zaidh-mech/project-zeno/assets/photos/20250816_165505.jpg

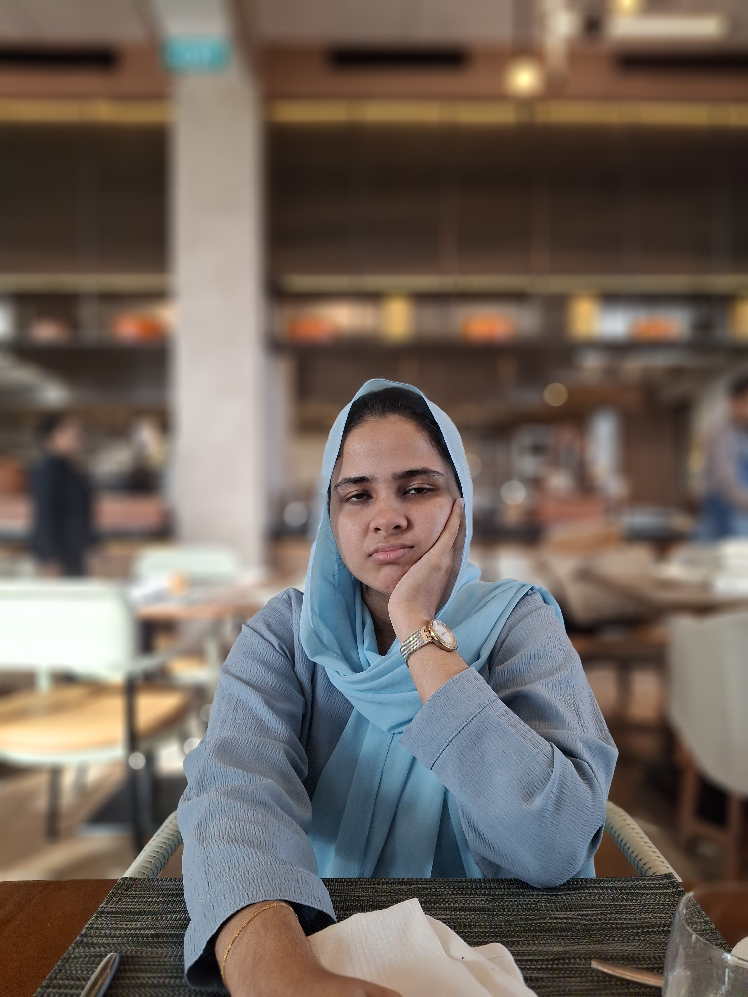
assets/photos/20250816_165505.jpg
