zaidh-mech/project-zeno/assets/photos/20250816_165511.jpg

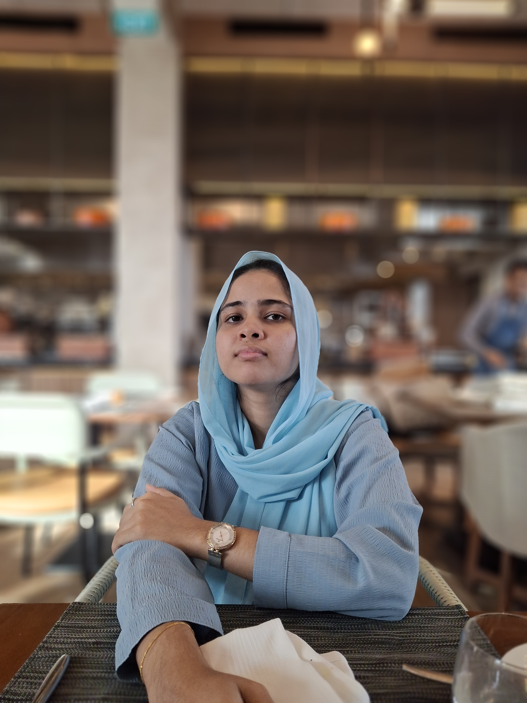
assets/photos/20250816_165511.jpg
