zaidh-mech/project-zeno/assets/photos/20250816_165538.jpg

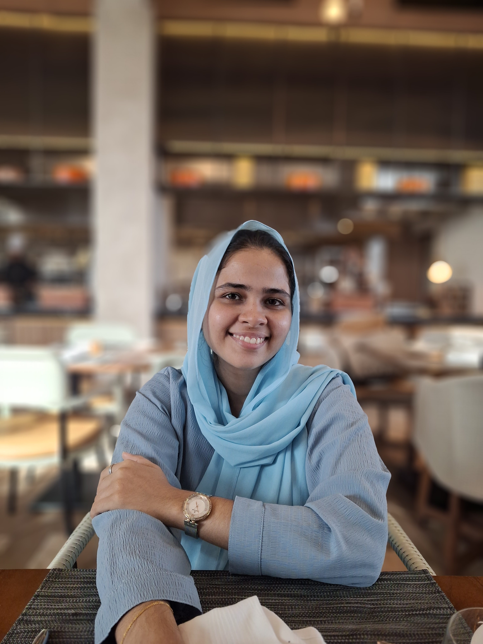
assets/photos/20250816_165538.jpg
