zaidh-mech/project-zeno/assets/photos/20250816_171857.jpg

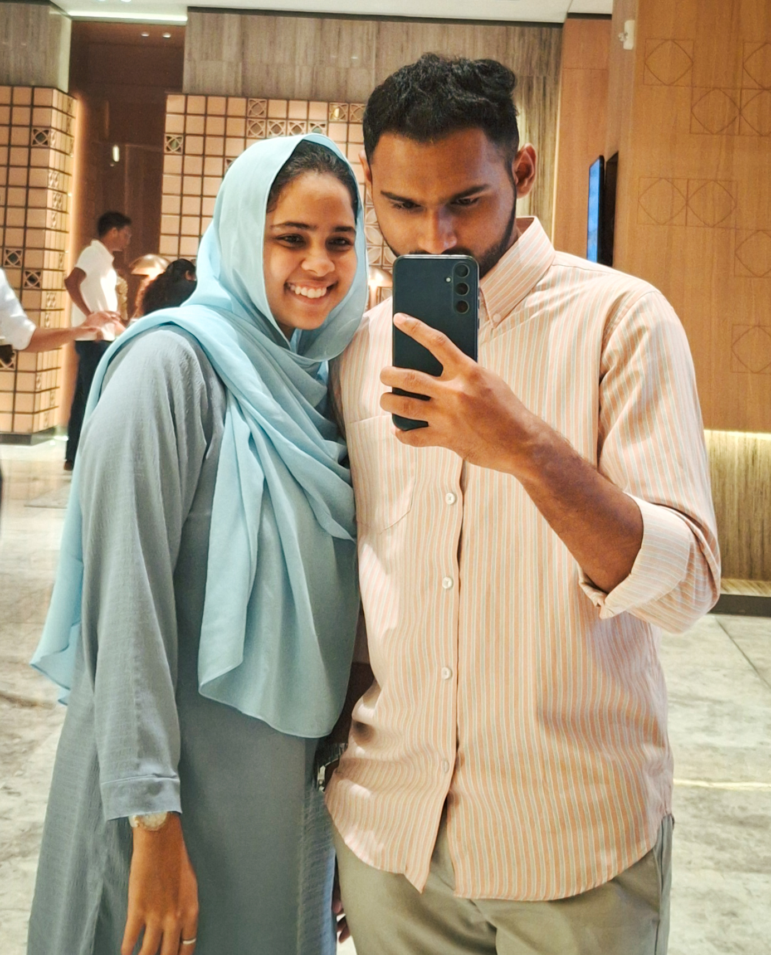
assets/photos/20250816_171857.jpg
