zaidh-mech/project-zeno/assets/photos/IMG-20231231-WA0020.jpg

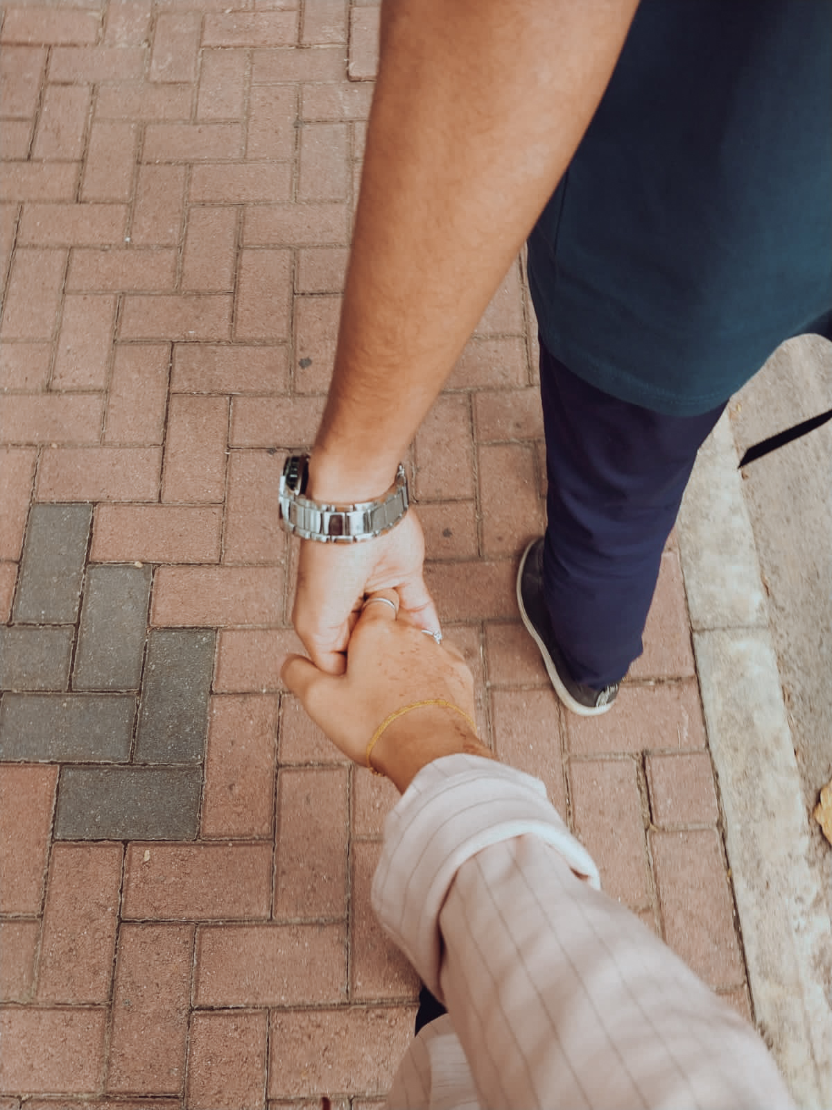
assets/photos/IMG-20231231-WA0020.jpg
