zaidh-mech/project-zeno/assets/photos/IMG-20240403-WA0015.jpg

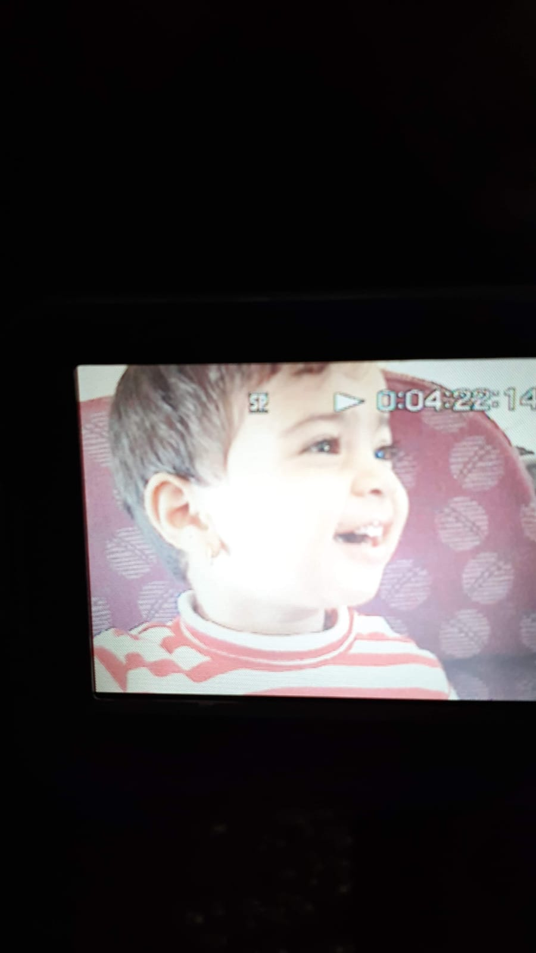
assets/photos/IMG-20240403-WA0015.jpg
