zaidh-mech/project-zeno/assets/photos/IMG-20240619-WA0054.jpg

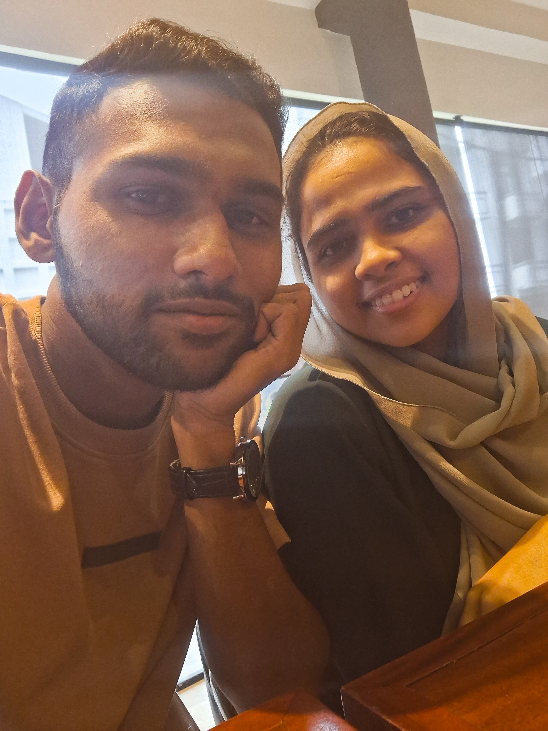
assets/photos/IMG-20240619-WA0054.jpg
