zaidh-mech/project-zeno/assets/photos/IMG-20241203-WA0028.jpg

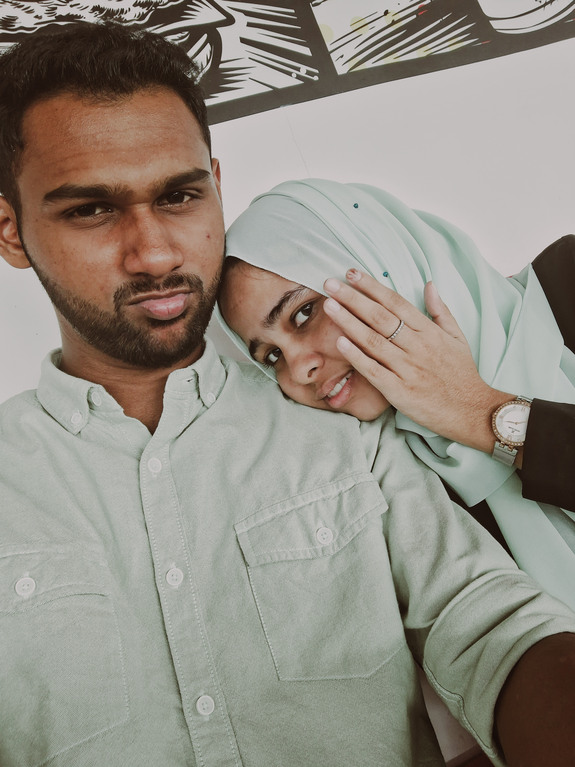
assets/photos/IMG-20241203-WA0028.jpg
