zaidh-mech/project-zeno/assets/photos/Snapchat-101565929.jpg

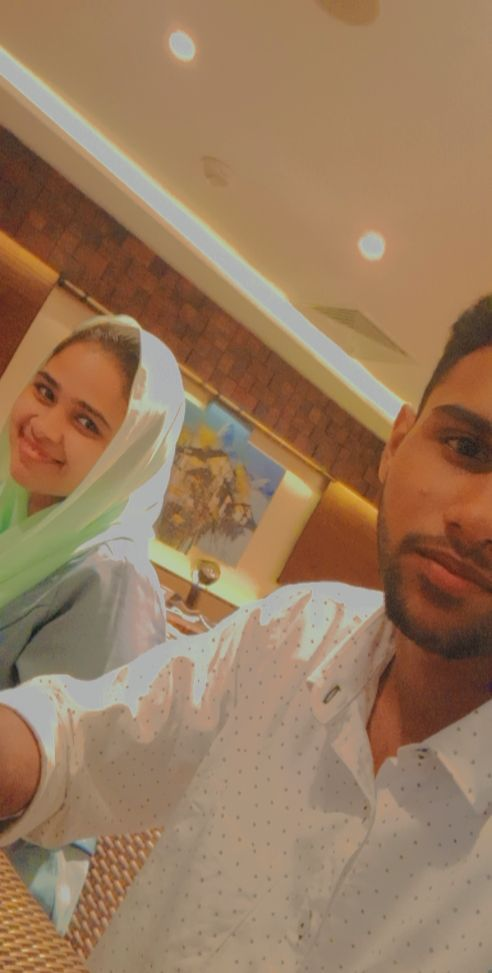
assets/photos/Snapchat-101565929.jpg
