zaidh-mech/project-zeno/assets/photos/Snapchat-125031793.jpg

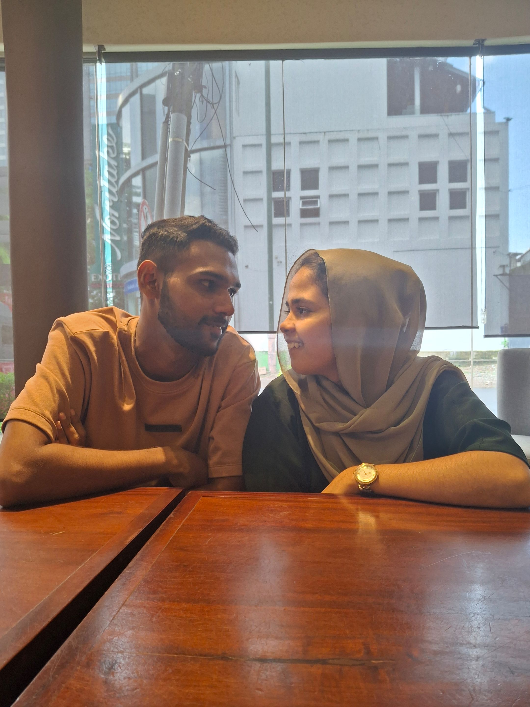
assets/photos/Snapchat-125031793.jpg
