zaidh-mech/project-zeno/assets/photos/Snapchat-195665847.jpg

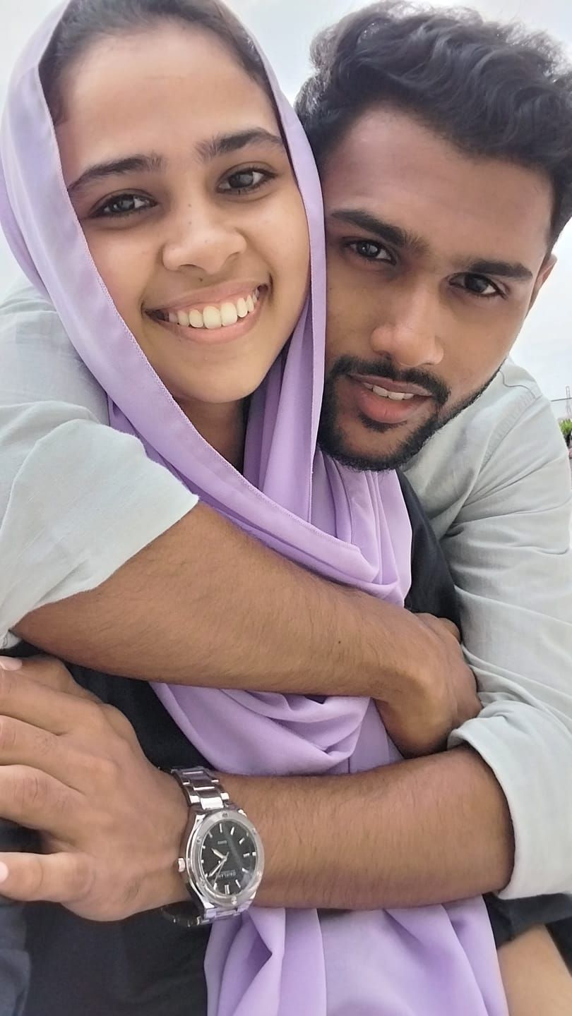
assets/photos/Snapchat-195665847.jpg
