zaidh-mech/project-zeno/assets/photos/Snapchat-261854260.jpg

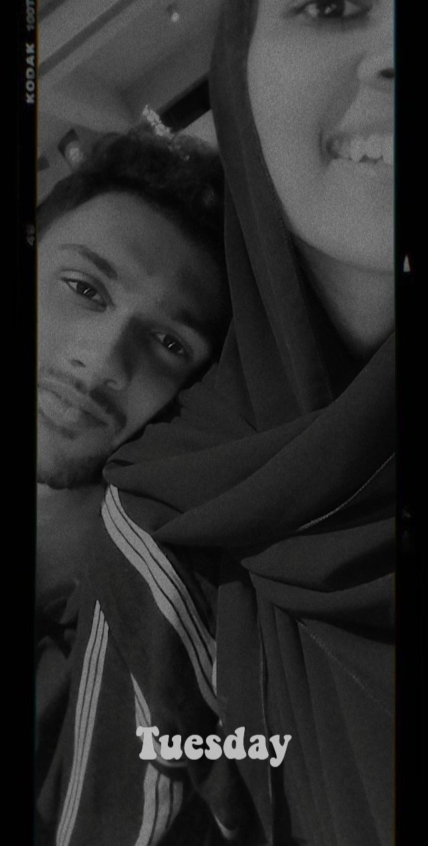
assets/photos/Snapchat-261854260.jpg
