zaidh-mech/project-zeno/assets/photos/Snapchat-302030129.jpg

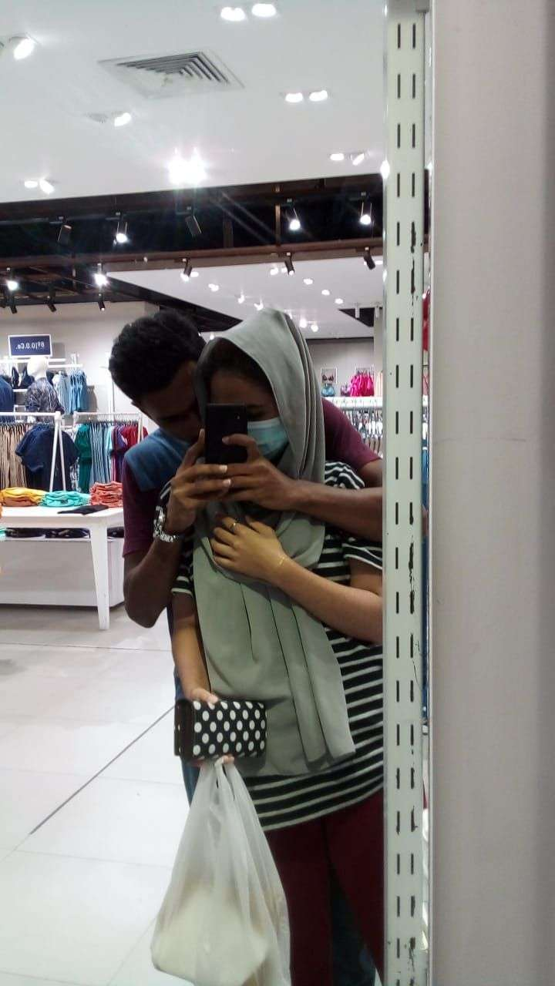
assets/photos/Snapchat-302030129.jpg
