zaidh-mech/project-zeno/assets/photos/Snapchat-348084734.jpg

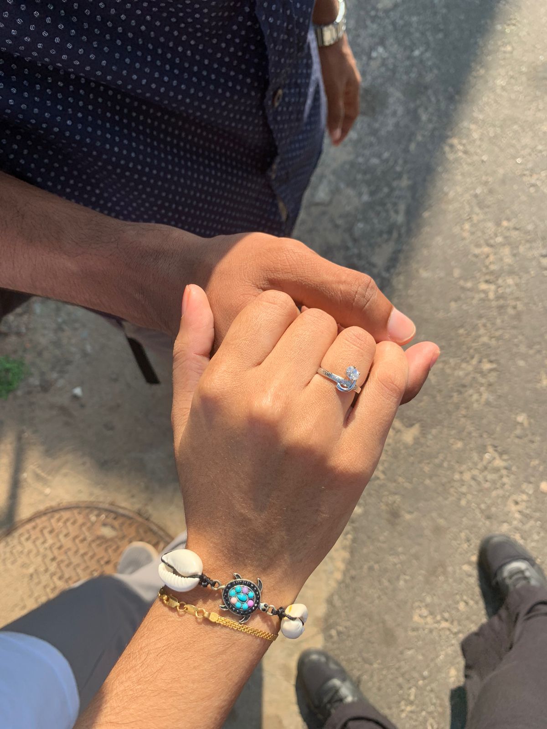
assets/photos/Snapchat-348084734.jpg
