zaidh-mech/project-zeno/assets/photos/Snapchat-446111282.jpg

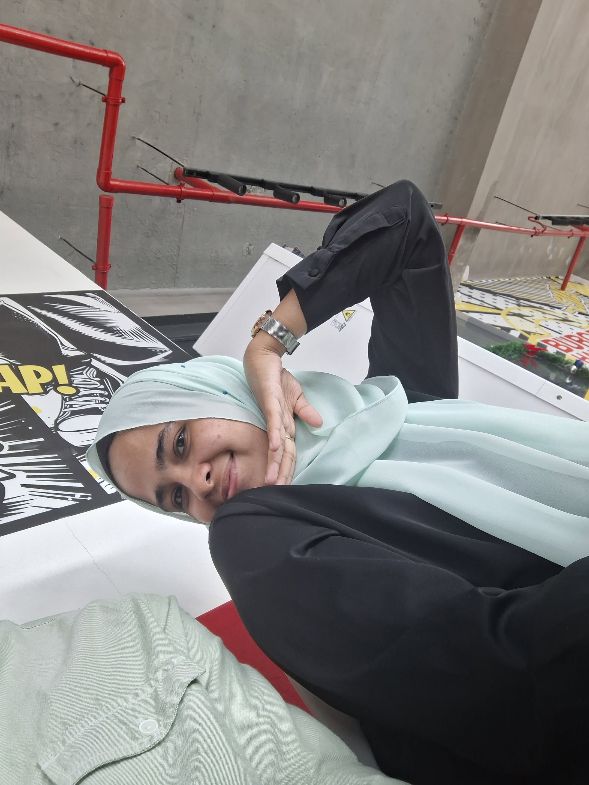
assets/photos/Snapchat-446111282.jpg
