zaidh-mech/project-zeno/assets/photos/Snapchat-537881204.jpg

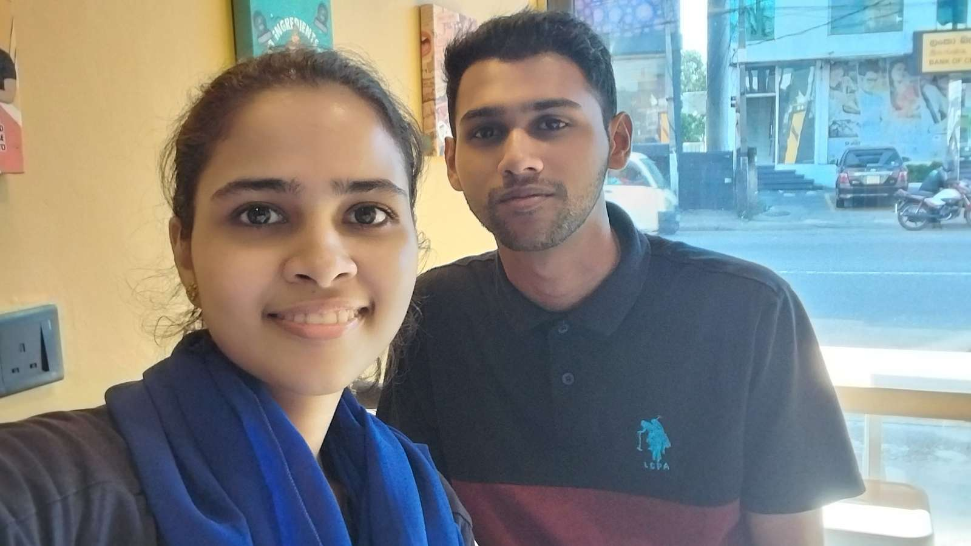
assets/photos/Snapchat-537881204.jpg
