zaidh-mech/project-zeno/assets/photos/Snapchat-637943176.jpg

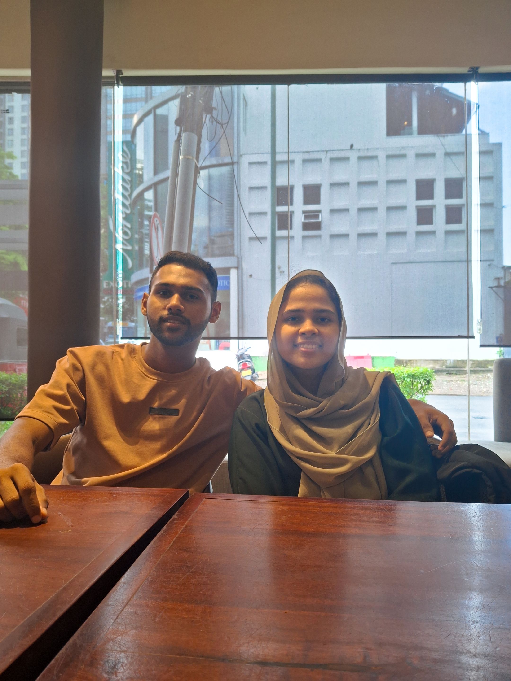
assets/photos/Snapchat-637943176.jpg
