zaidh-mech/project-zeno/assets/photos/Snapchat-755938516.jpg

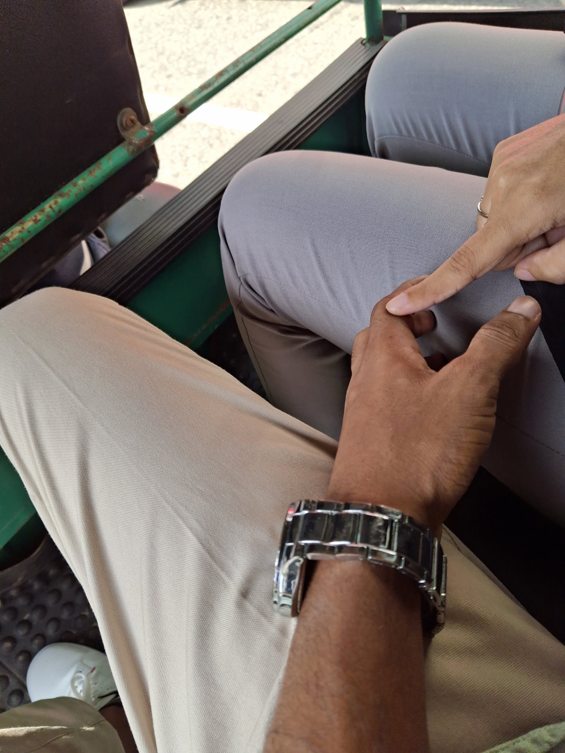
assets/photos/Snapchat-755938516.jpg
