zaidh-mech/project-zeno/assets/photos/Snapchat-759489266.jpg

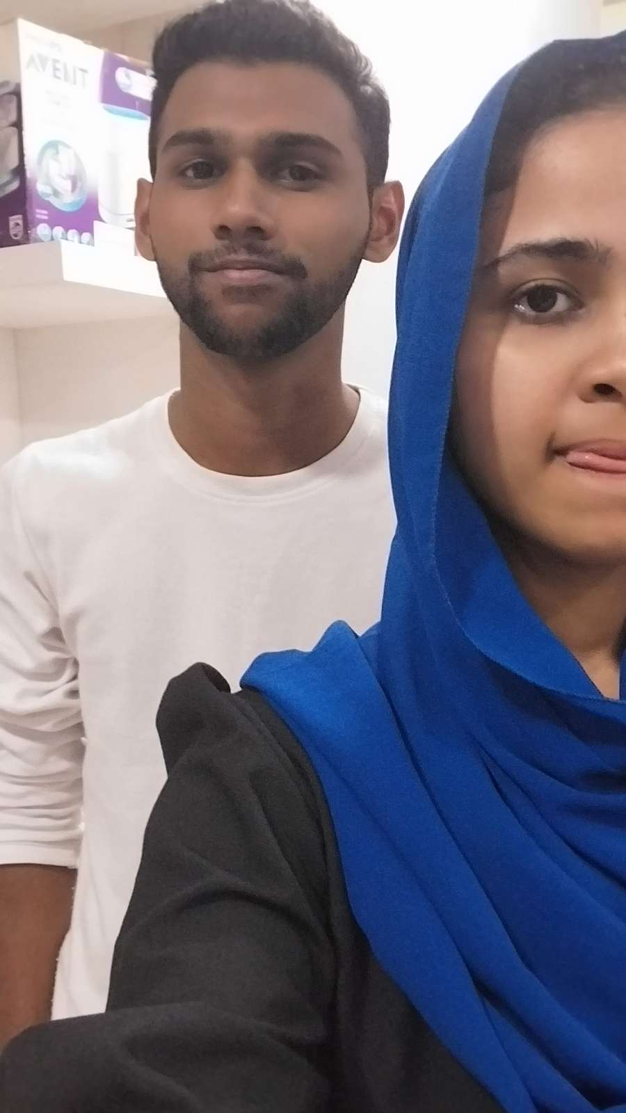
assets/photos/Snapchat-759489266.jpg
