zaidh-mech/project-zeno/assets/photos/Snapchat-868171429.jpg

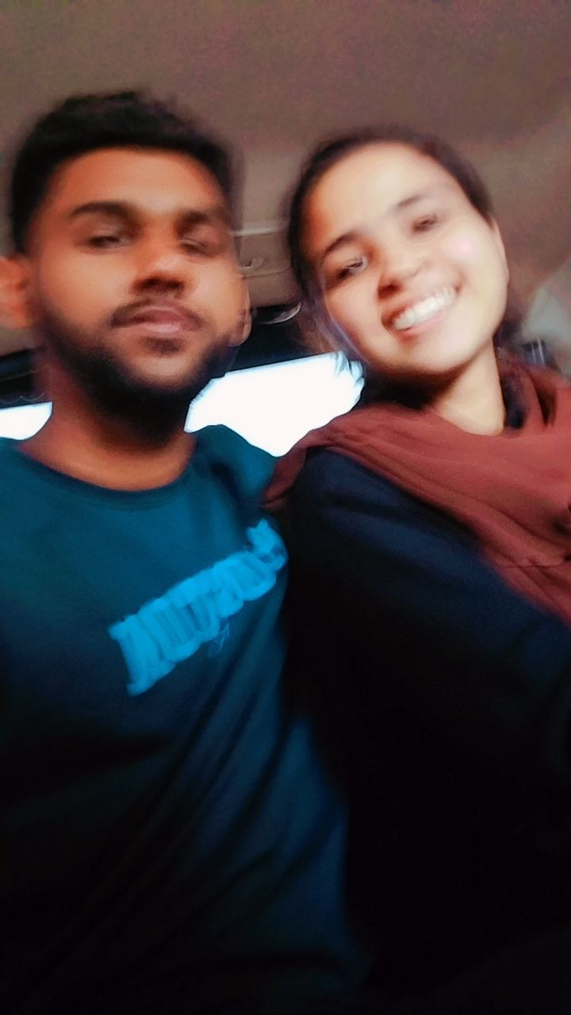
assets/photos/Snapchat-868171429.jpg
