zaidh-mech/project-zeno/assets/photos/Snapchat-1000629672.jpg

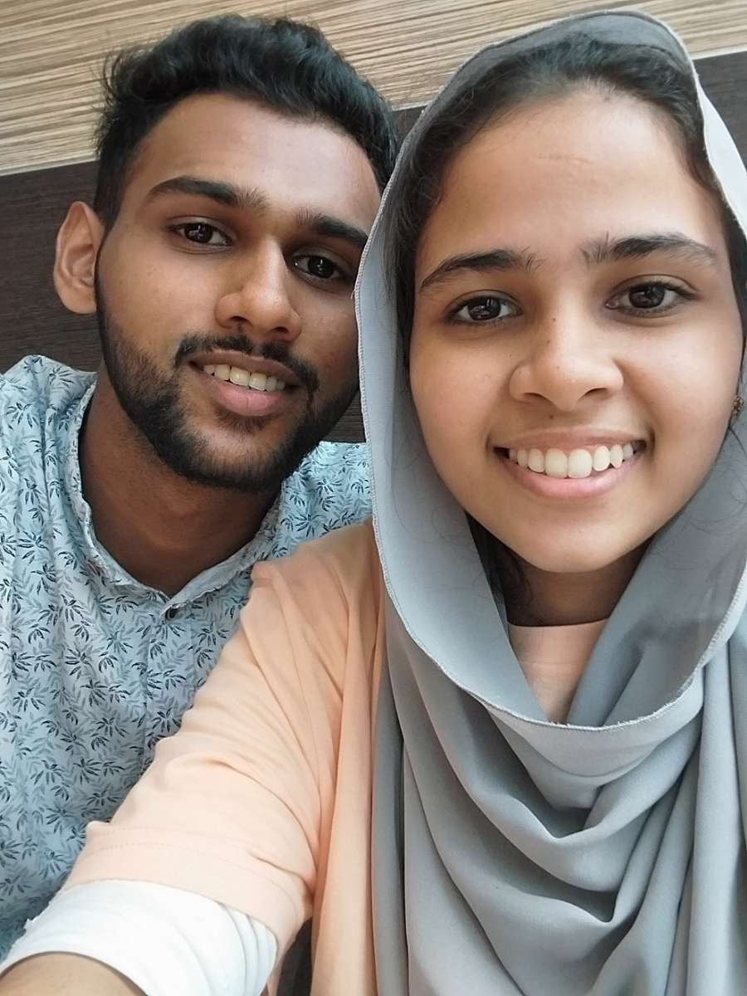
assets/photos/Snapchat-1000629672.jpg
