zaidh-mech/project-zeno/assets/photos/Snapchat-1169559502.jpg

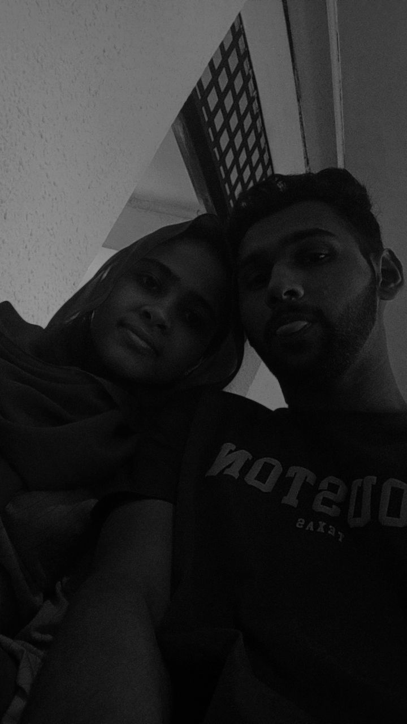
assets/photos/Snapchat-1169559502.jpg
