zaidh-mech/project-zeno/assets/photos/Snapchat-1356561112.jpg

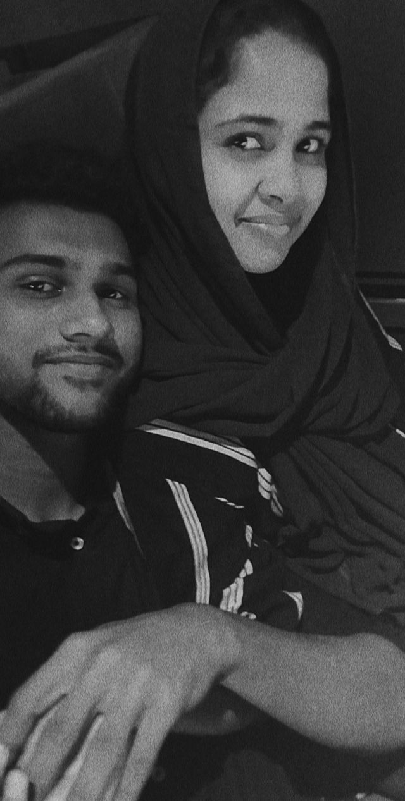
assets/photos/Snapchat-1356561112.jpg
