zaidh-mech/project-zeno/assets/photos/Snapchat-1552943826.jpg

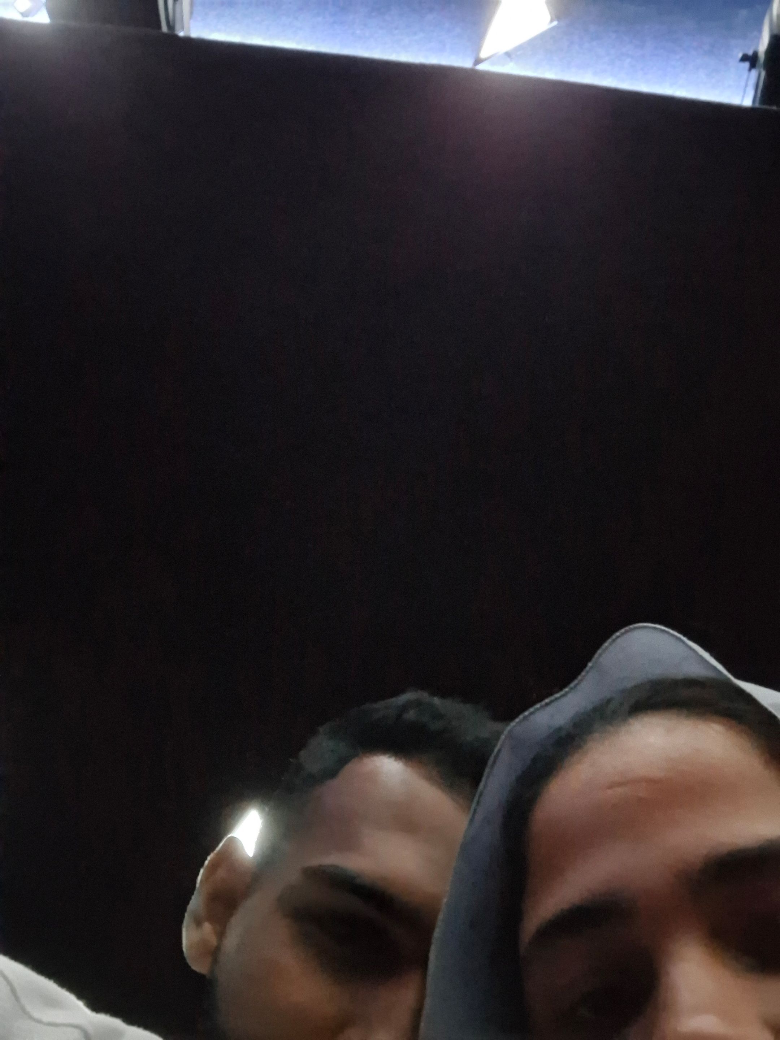
assets/photos/Snapchat-1552943826.jpg
