zaidh-mech/project-zeno/assets/photos/Snapchat-1667827849.jpg

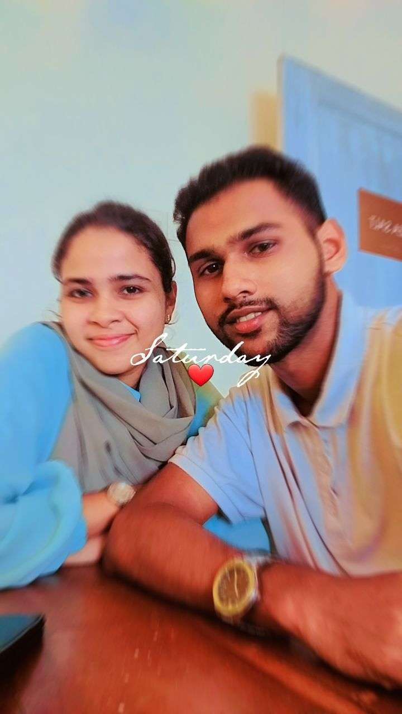
assets/photos/Snapchat-1667827849.jpg
