zaidh-mech/project-zeno/assets/photos/Snapchat-1719029851.jpg

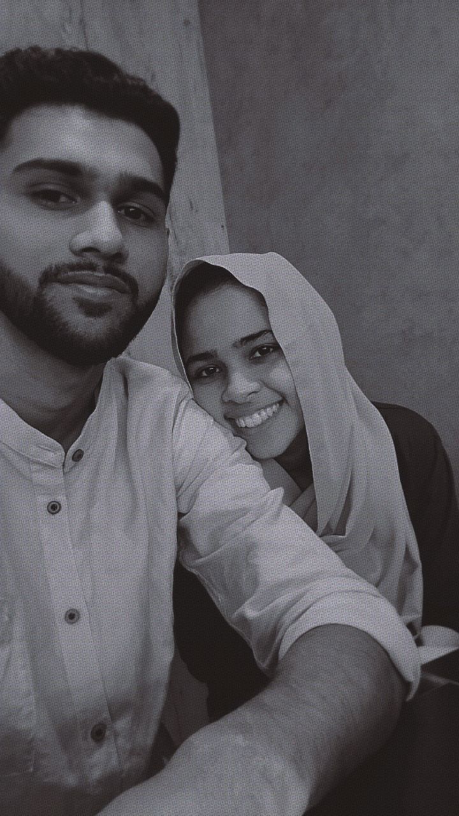
assets/photos/Snapchat-1719029851.jpg
