zaidh-mech/project-zeno/assets/photos/Snapchat-1755354417.jpg

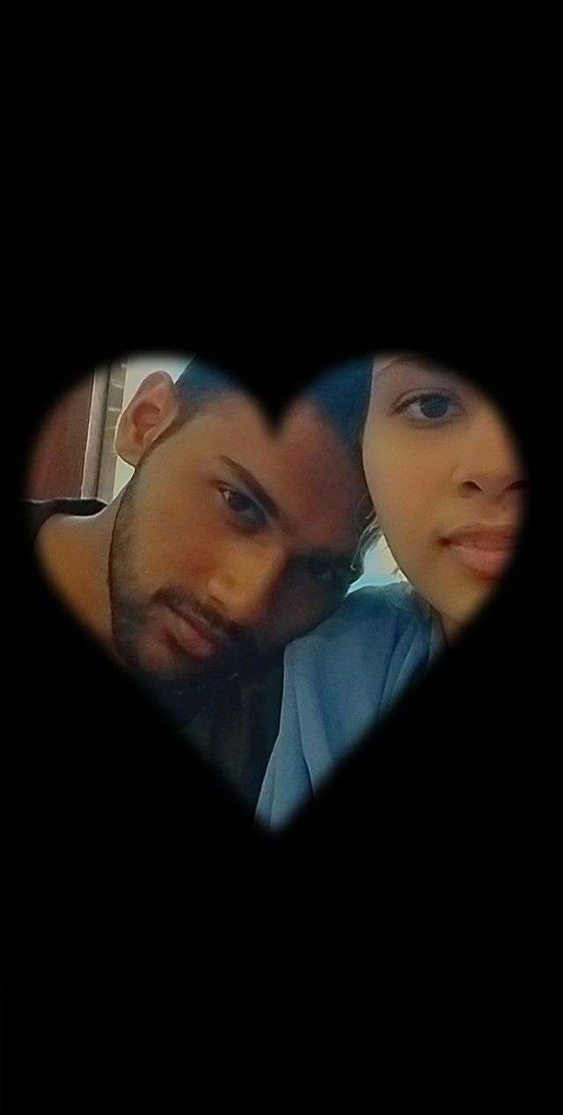
assets/photos/Snapchat-1755354417.jpg
