zaidh-mech/project-zeno/assets/photos/Snapchat-1938630685.jpg

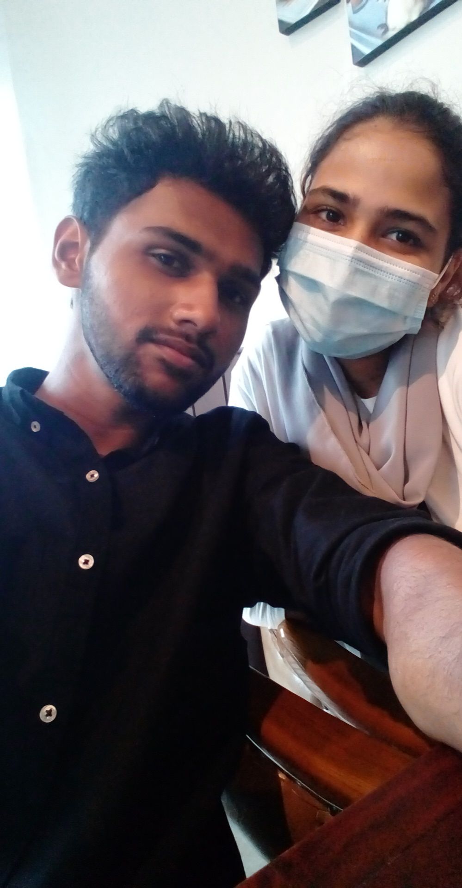
assets/photos/Snapchat-1938630685.jpg
