zaidh-mech/project-zeno/assets/photos/Snapchat-1975126700.jpg

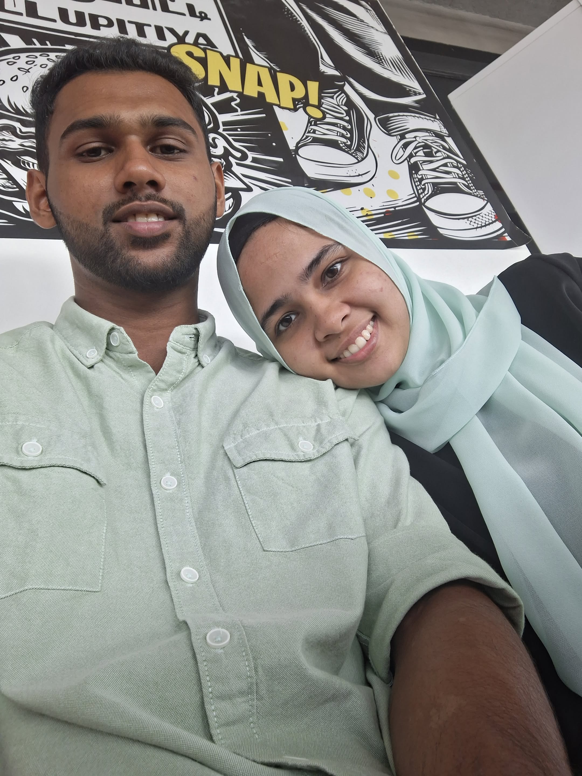
assets/photos/Snapchat-1975126700.jpg
