zaidh-mech/project-zeno/assets/photos/Snapchat-2021210493.jpg

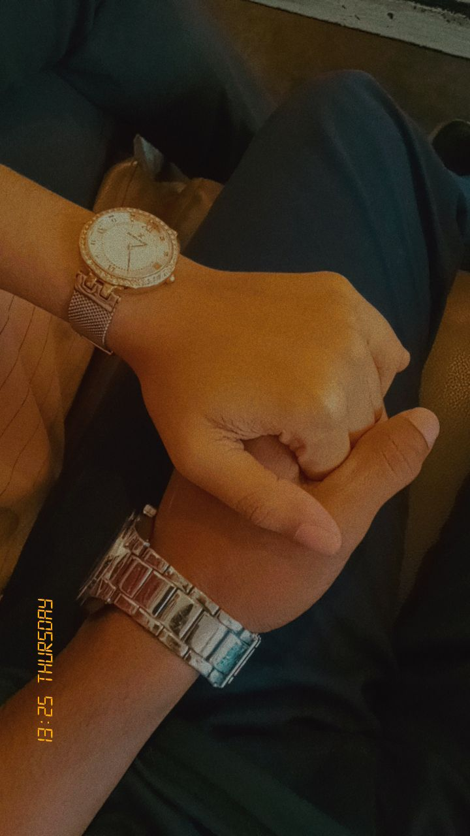
assets/photos/Snapchat-2021210493.jpg
