zaidh-mech/project-zeno/assets/photos/Snapchat-2032227030.jpg

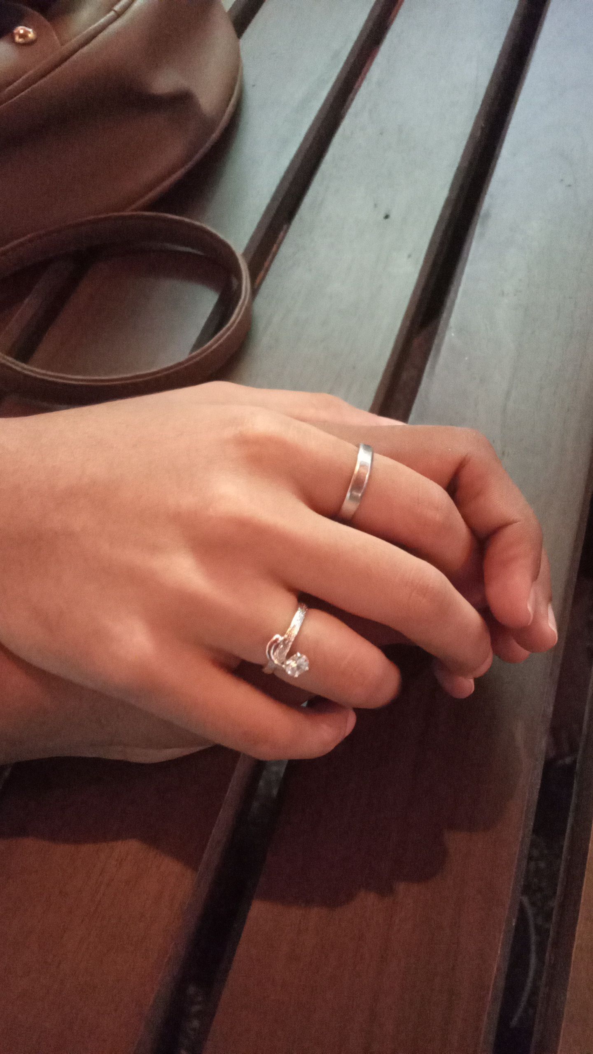
assets/photos/Snapchat-2032227030.jpg
