zaidh-mech/project-zeno/assets/photos/Snapchat-2075881520.jpg

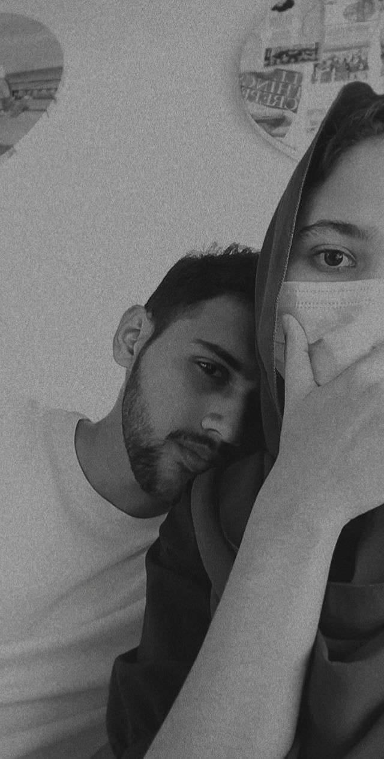
assets/photos/Snapchat-2075881520.jpg
