zaidh-mech/project-zeno/assets/screenshots/Screenshot 2026-09-28 134337.png

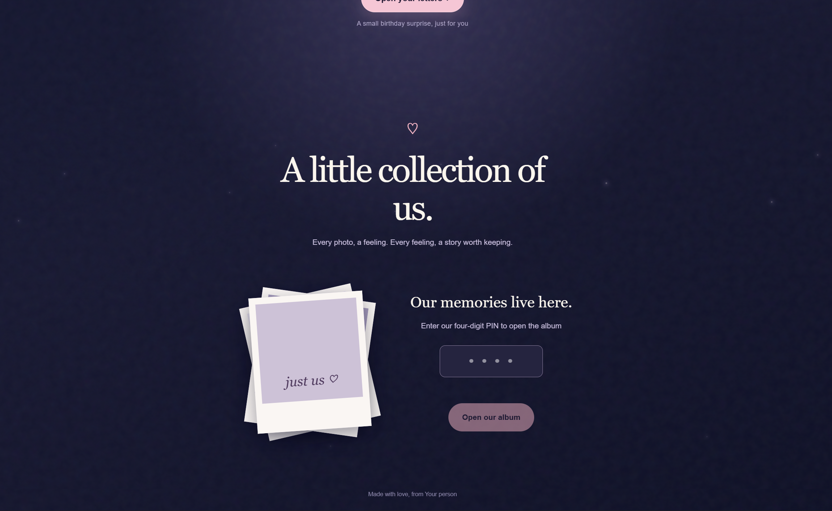
assets/screenshots/Screenshot 2026-09-28 134337.png
