zaidh-mech/project-zeno/assets/screenshots/Screenshot 2026-10-01 145643.png

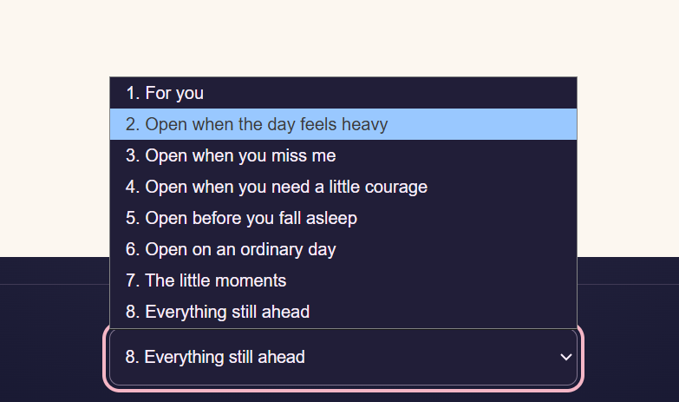
assets/screenshots/Screenshot 2026-10-01 145643.png
