zaidh-mech/project-zeno/assets/screenshots/Screenshot 2026-10-02 182400.png

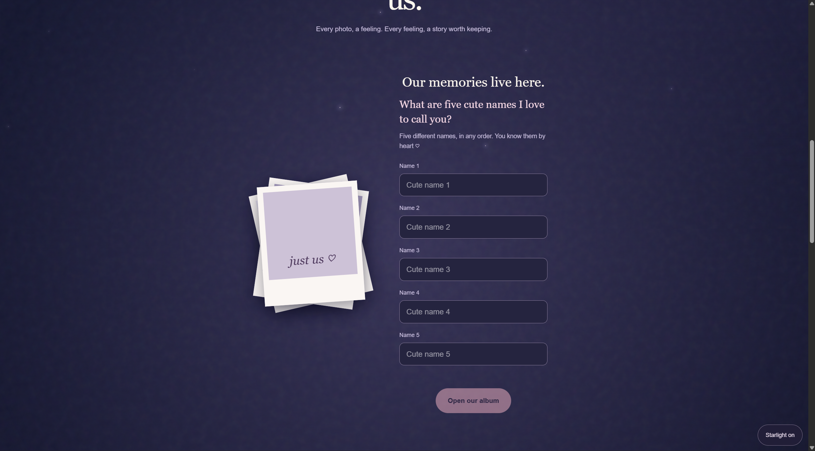
assets/screenshots/Screenshot 2026-10-02 182400.png
