zaidh-mech/project-zeno/companion/drawings/02_Rear_ports.png

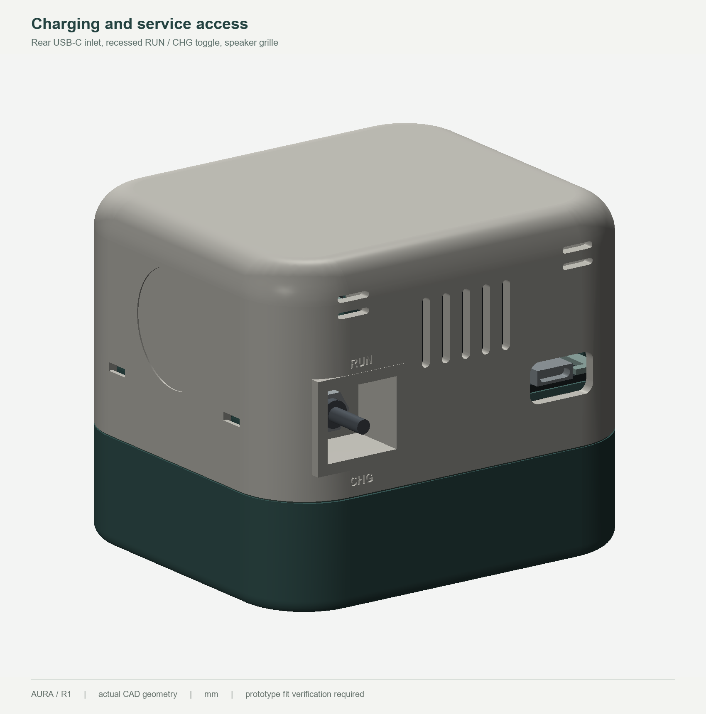
companion/drawings/02_Rear_ports.png
