zaidh-mech/project-zeno/companion/drawings/03_Internal_layout.png

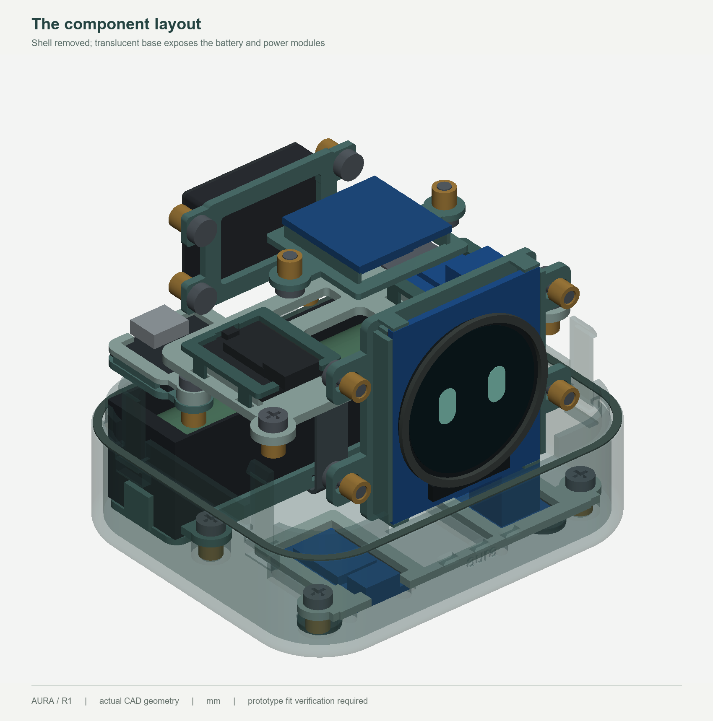
companion/drawings/03_Internal_layout.png
