zaidh-mech/project-zeno/companion/drawings/04_Exploded.png

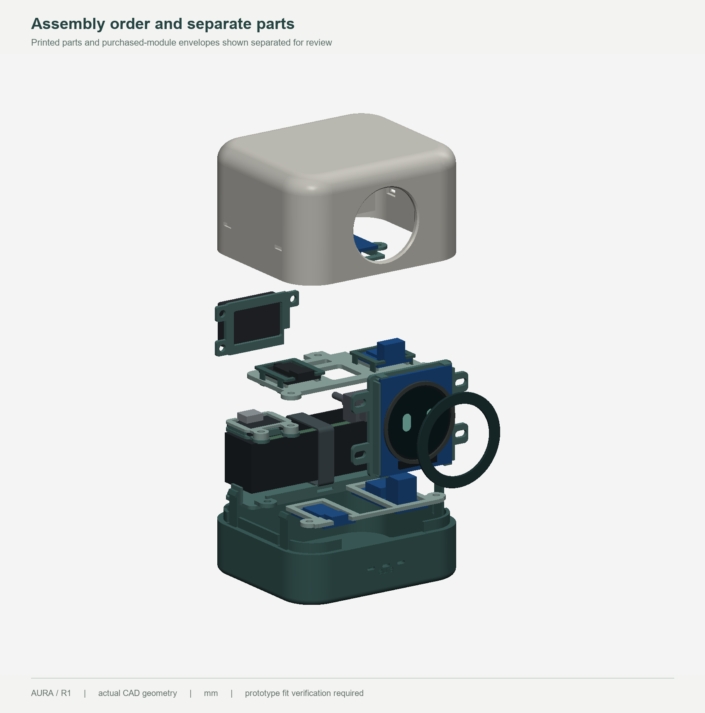
companion/drawings/04_Exploded.png
