zaidh-mech/project-zeno/companion/drawings/05_Cutaway.png

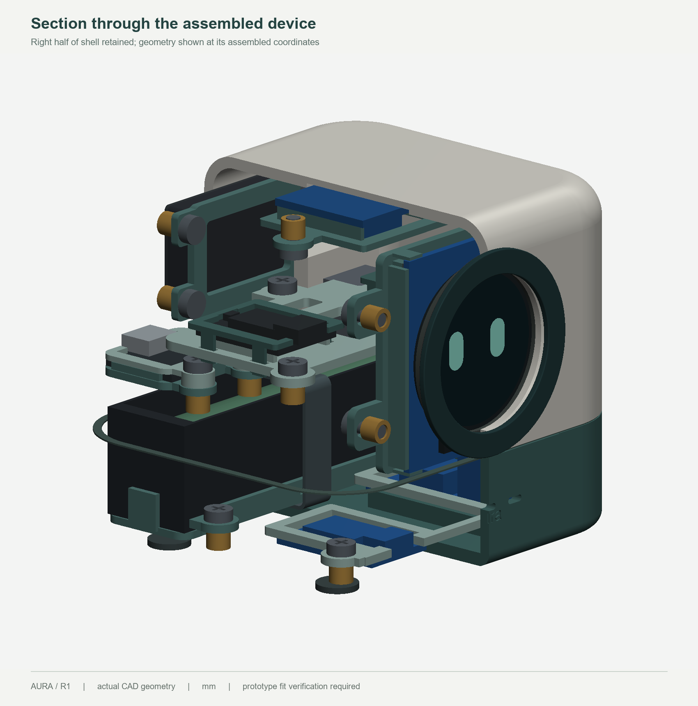
companion/drawings/05_Cutaway.png
