zaidh-mech/project-zeno/companion/drawings/06_General_arrangement.png

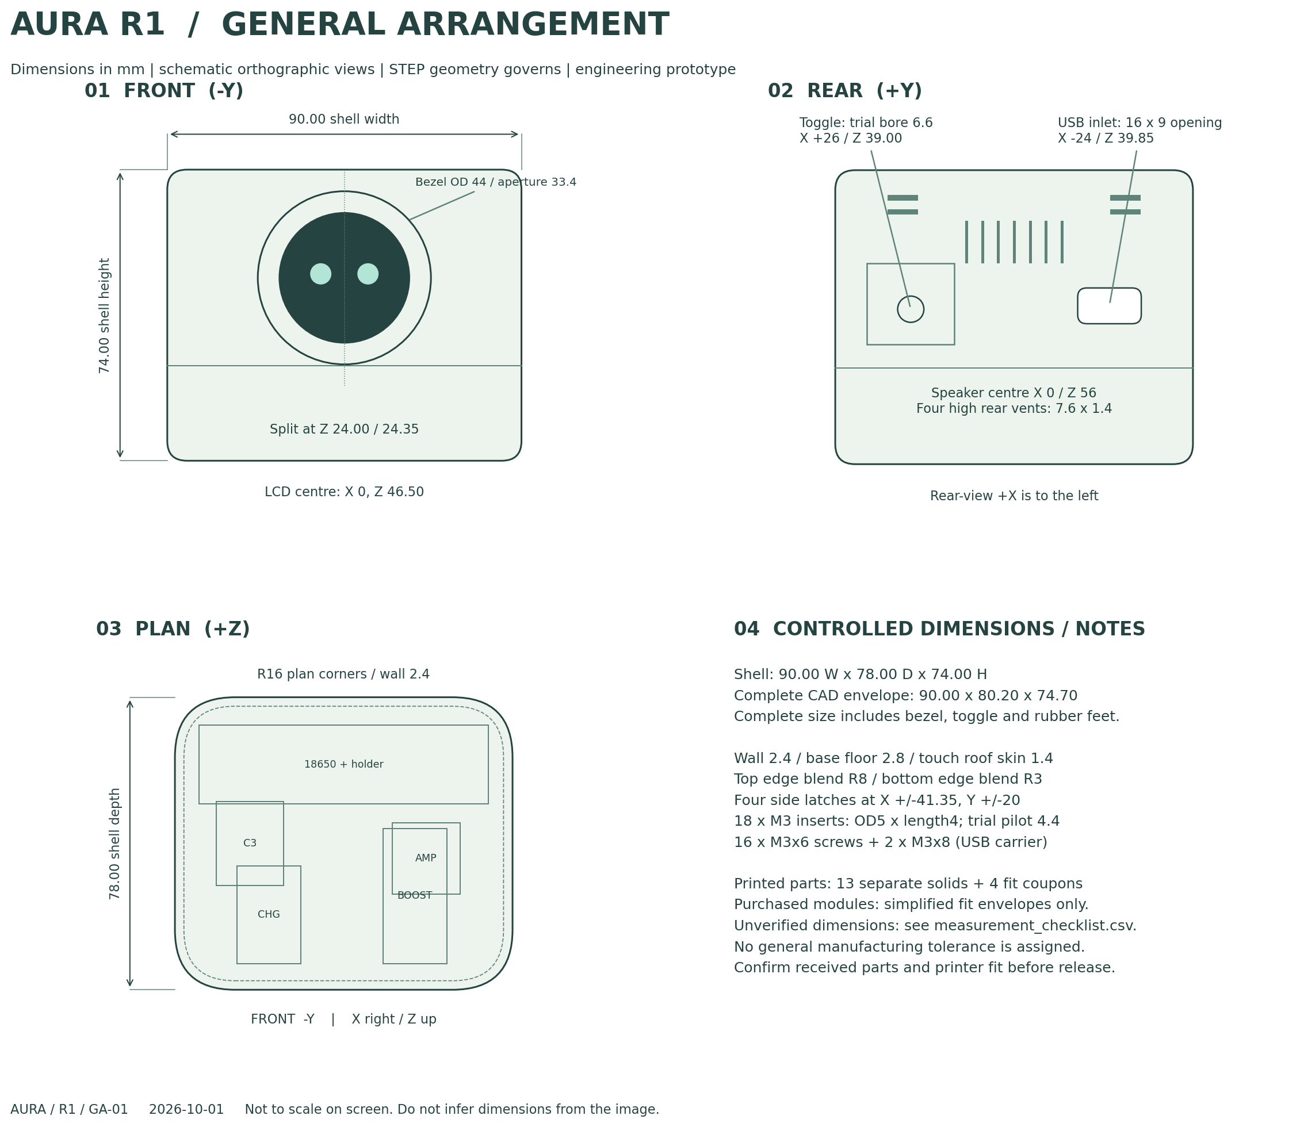
companion/drawings/06_General_arrangement.png
