zaidh-mech/project-zeno/companion/drawings/07_Snap_and_insert_details.png

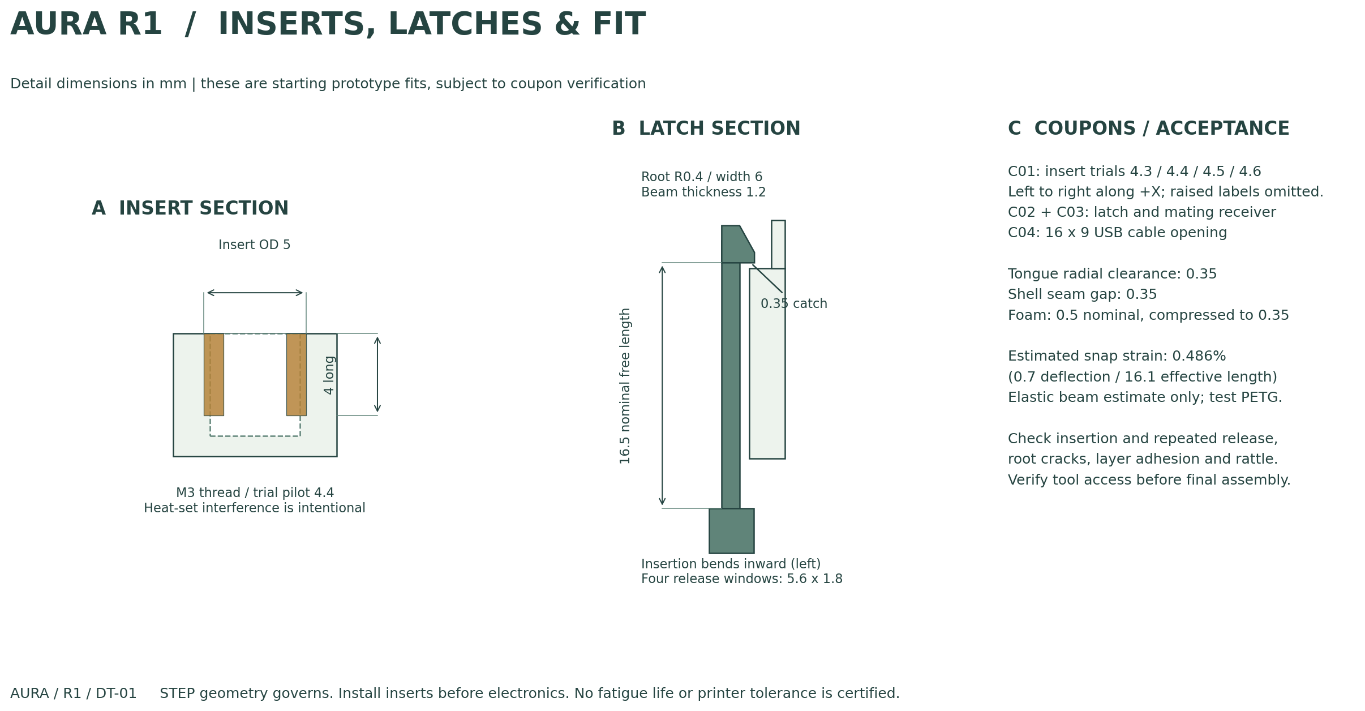
companion/drawings/07_Snap_and_insert_details.png
