zaidh-mech/project-zeno/companion/drawings/08_Power_connections.png

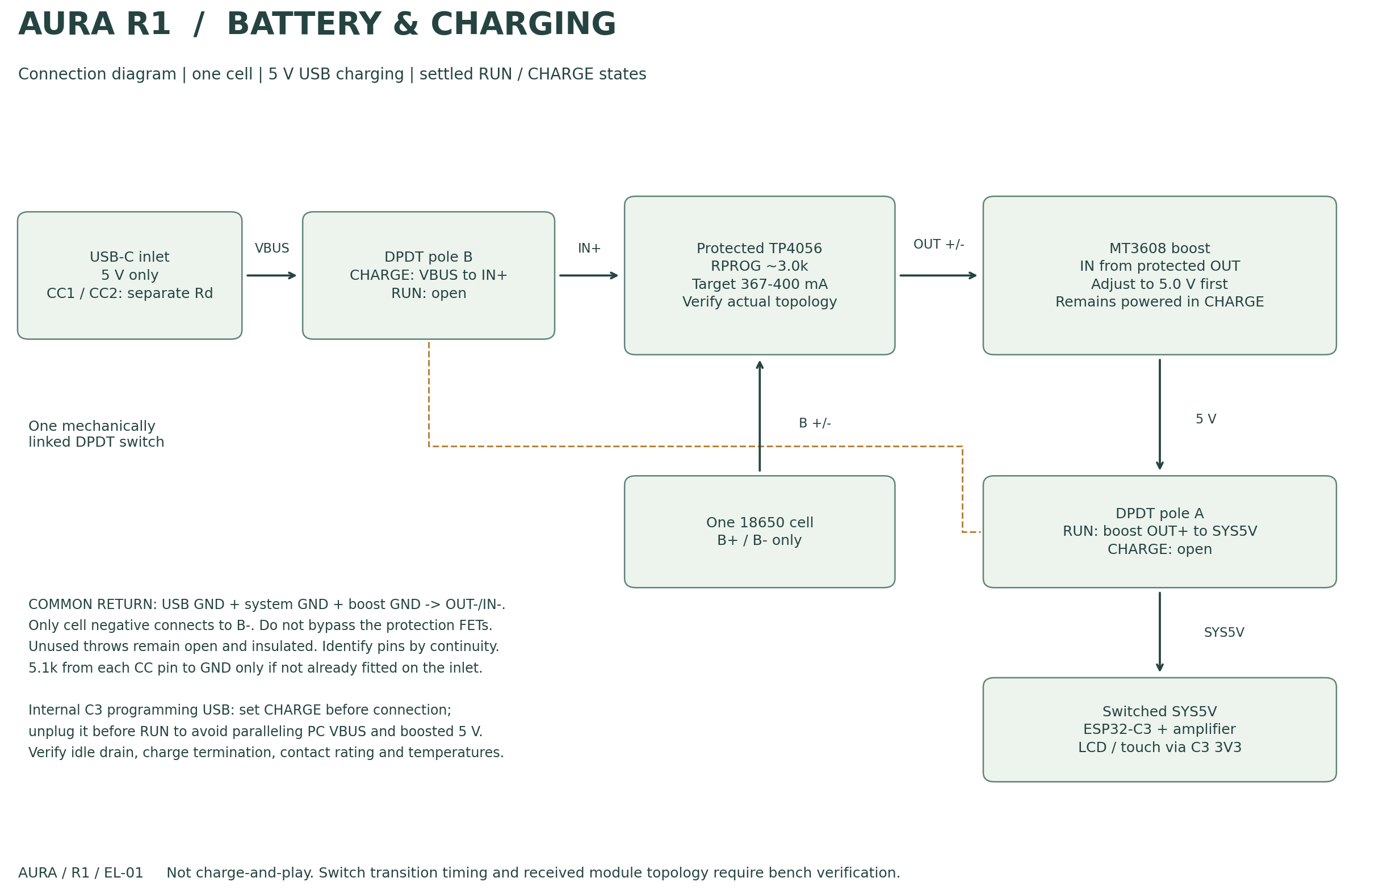
companion/drawings/08_Power_connections.png
