zaidh-mech/project-zeno/companion/parts/coupons/C01_Insert_bores_4p3_4p4_4p5_4p6.step

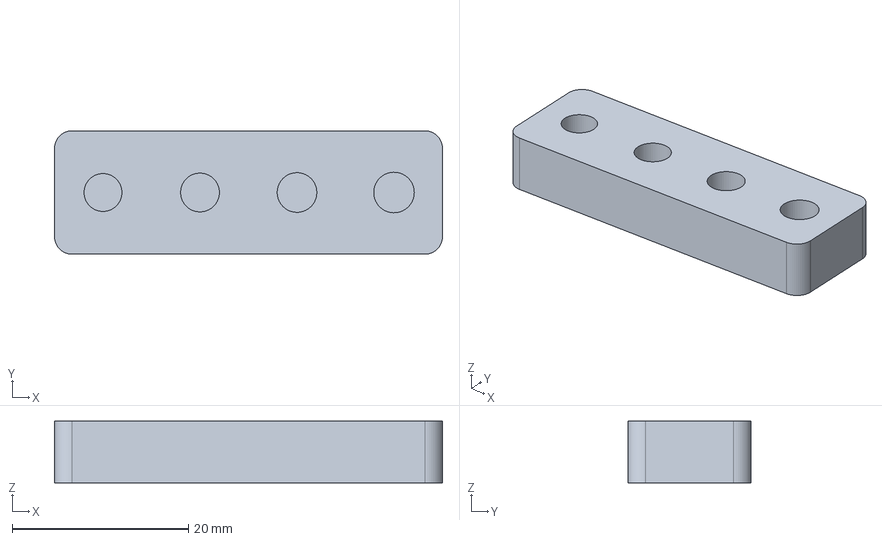
[picture p69: CAD file, 2026-10-05]
companion/parts/coupons/C01_Insert_bores_4p3_4p4_4p5_4p6.step
44.0 x 14.0 x 7.00 mm
