zaidh-mech/project-zeno/companion/parts/electronics/E08_MT3608_ML2060.step

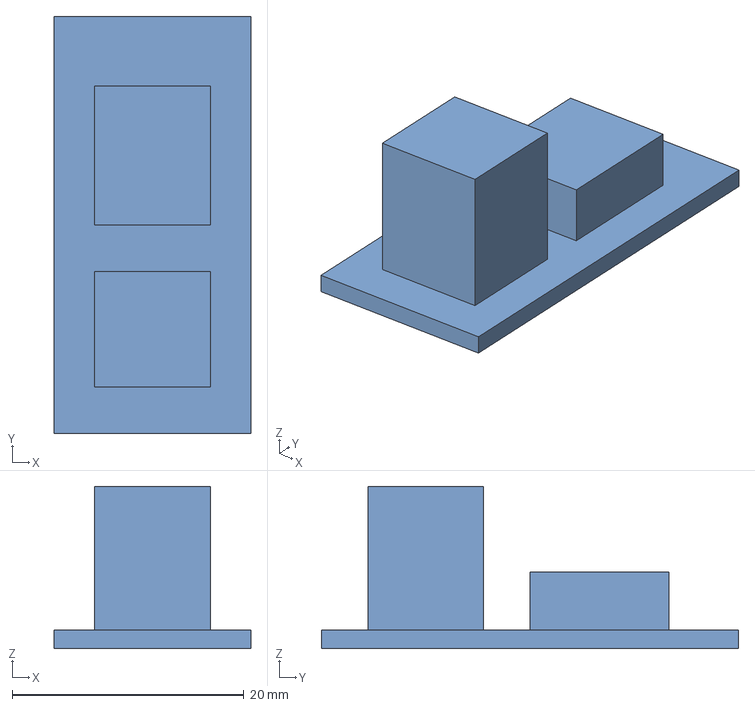
[picture p70: CAD file, 2026-10-05]
companion/parts/electronics/E08_MT3608_ML2060.step
17.0 x 36.0 x 14.0 mm
