zaidh-mech/project-zeno/companion/parts/hardware/H92_USB_insert_1.step

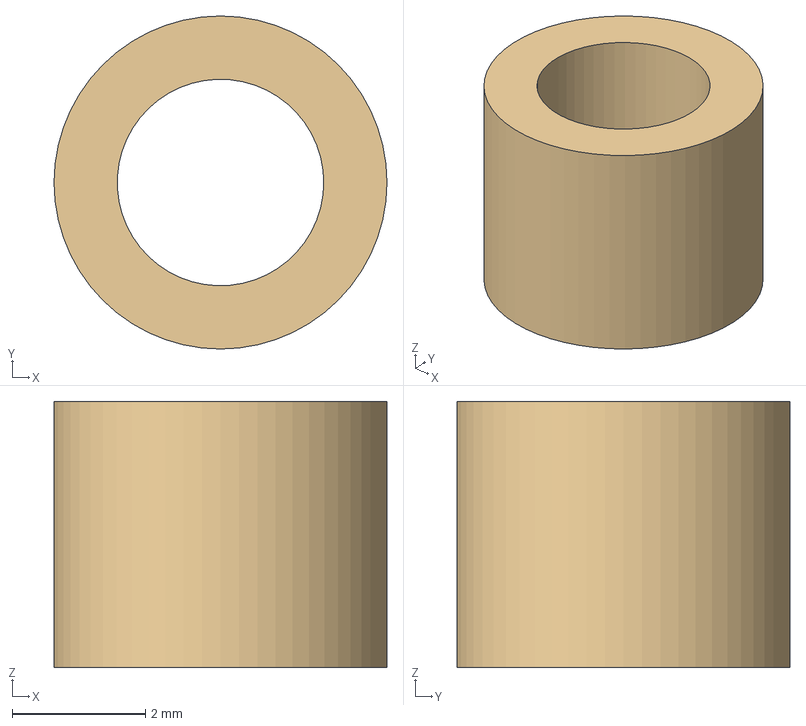
[picture p71: CAD file, 2026-10-05]
companion/parts/hardware/H92_USB_insert_1.step
5.00 x 5.00 x 4.00 mm
