zaidh-mech/project-zeno/companion/parts/printed/P08_Power_board_retainer.step

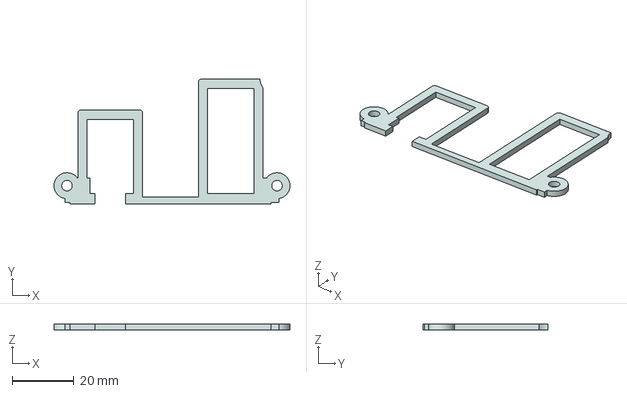
[picture p72: CAD file, 2026-10-05]
companion/parts/printed/P08_Power_board_retainer.step
76.4 x 40.4 x 1.80 mm
