zaidh-mech/project-zeno/companion/parts/coupons/C02_Snap_latch.stl

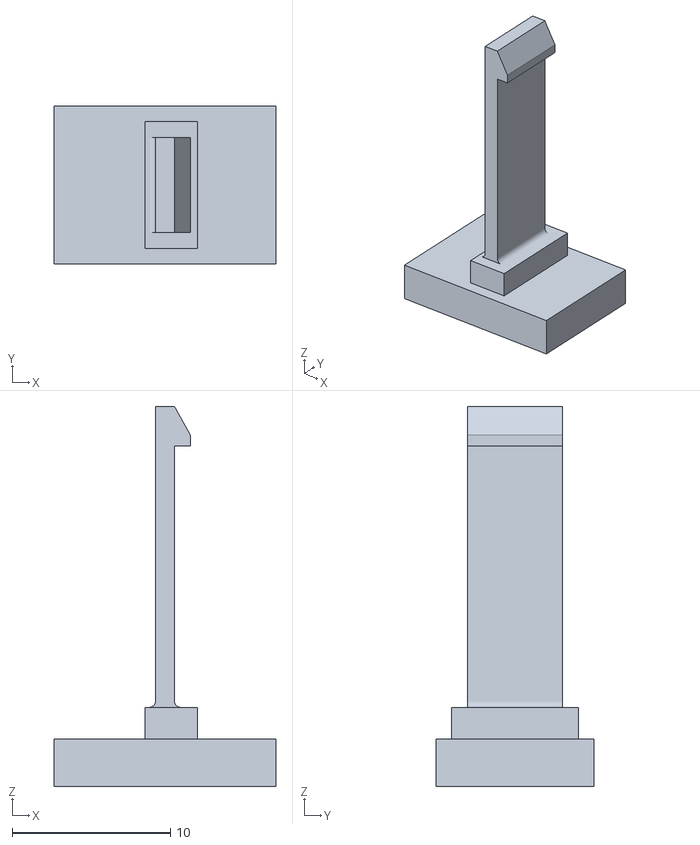
[picture p73: CAD file, 2026-10-05]
companion/parts/coupons/C02_Snap_latch.stl
14.0 x 10.0 x 24.0
