zaidh-mech/project-zeno/companion/parts/electronics/E06_3020_speaker_PAL36.step

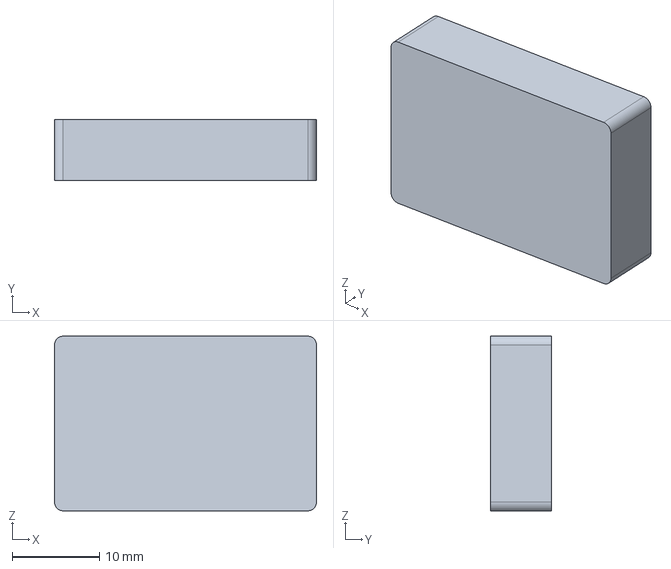
[picture p74: CAD file, 2026-10-05]
companion/parts/electronics/E06_3020_speaker_PAL36.step
30.0 x 7.00 x 20.0 mm
