zaidh-mech/project-zeno/companion/parts/hardware/H04_LCD_edge_pad_-18_66.5.step

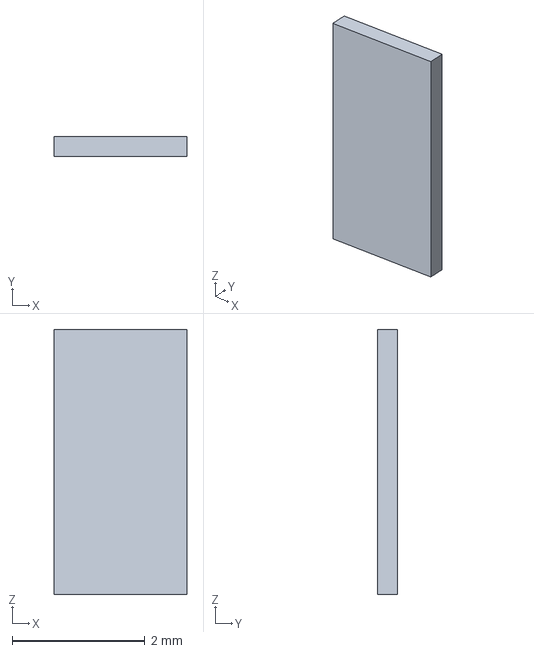
[picture p75: CAD file, 2026-10-05]
companion/parts/hardware/H04_LCD_edge_pad_-18_66.5.step
2.00 x 0.3 x 4.00 mm
