zaidh-mech/project-zeno/companion/STL/P10_Touch_retaining_frame.stl

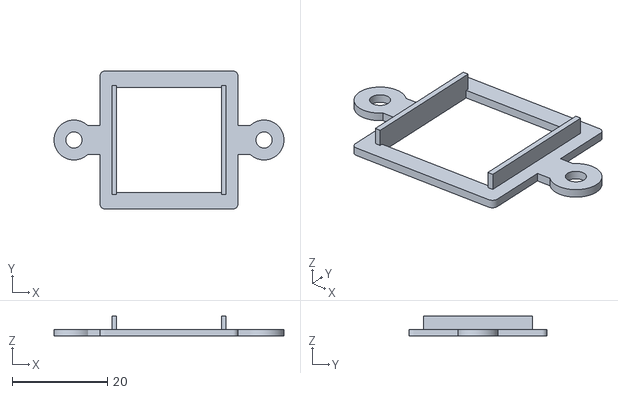
[picture p76: CAD file, 2026-10-05]
companion/STL/P10_Touch_retaining_frame.stl
48.4 x 29.0 x 4.20
