zaidh-mech/project-zeno/companion/parts/electronics/E04_MAX98357_MD0860.step

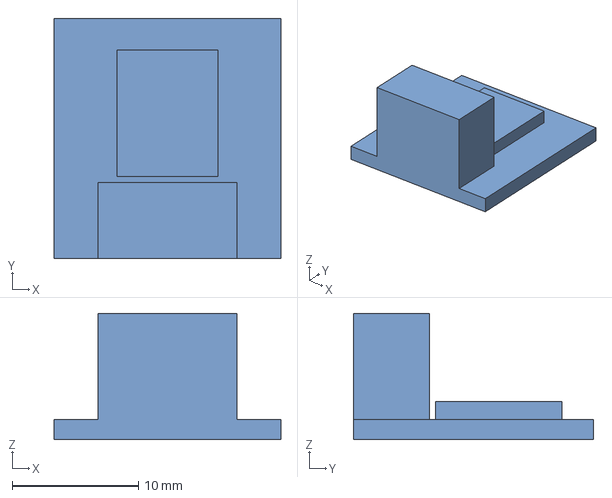
[picture p77: CAD file, 2026-10-05]
companion/parts/electronics/E04_MAX98357_MD0860.step
18.0 x 19.0 x 10.0 mm
