zaidh-mech/project-zeno/companion/parts/hardware/H08_Power_pad_19_-1.step

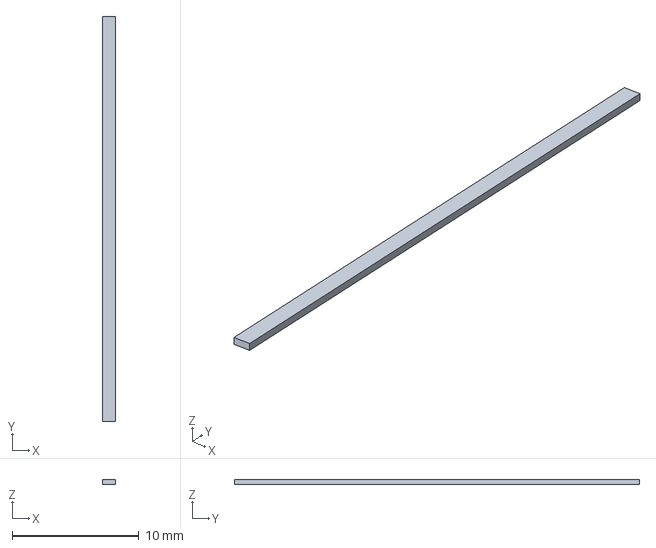
[picture p78: CAD file, 2026-10-05]
companion/parts/hardware/H08_Power_pad_19_-1.step
1.00 x 32.0 x 0.4 mm
