zaidh-mech/project-zeno/companion/parts/printed/P02_Snap_base.step

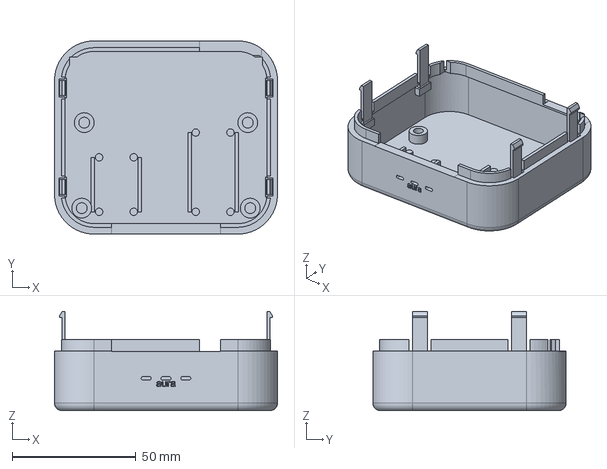
[picture p79: CAD file, 2026-10-05]
companion/parts/printed/P02_Snap_base.step
90.0 x 78.0 x 40.0 mm
