zaidh-mech/project-zeno/companion/STL/P05_Electronics_deck.stl

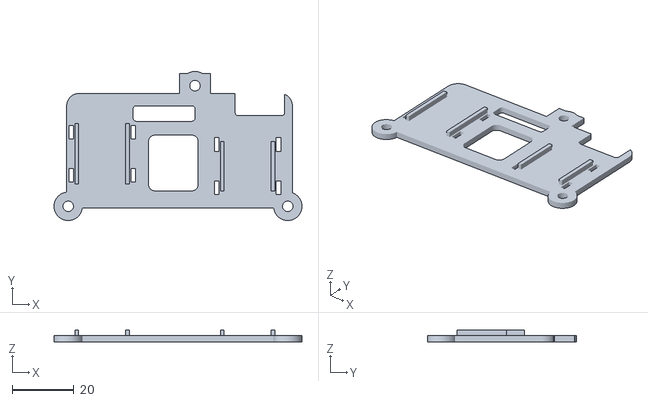
[picture p80: CAD file, 2026-10-05]
companion/STL/P05_Electronics_deck.stl
80.2 x 48.2 x 3.80
