zaidh-mech/project-zeno/companion/parts/electronics/E02_LCD_panel_reference.step

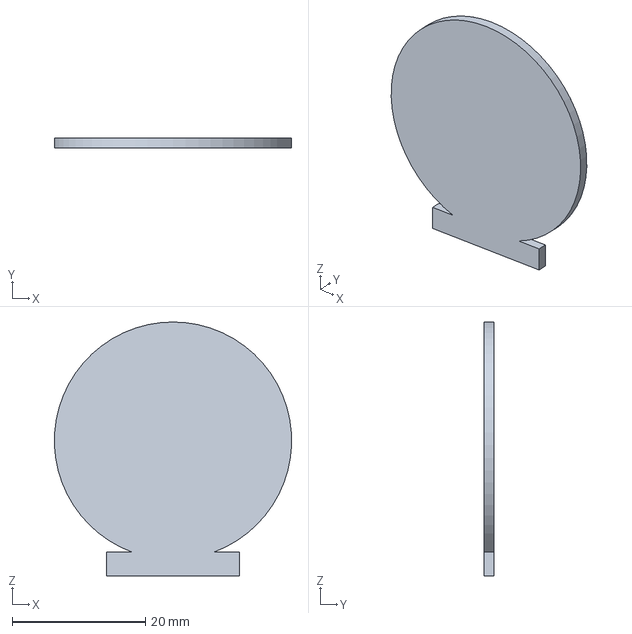
[picture p81: CAD file, 2026-10-05]
companion/parts/electronics/E02_LCD_panel_reference.step
35.6 x 1.50 x 38.1 mm
