zaidh-mech/project-zeno/companion/parts/electronics/E12_MTS202_BU0014_provisional.step

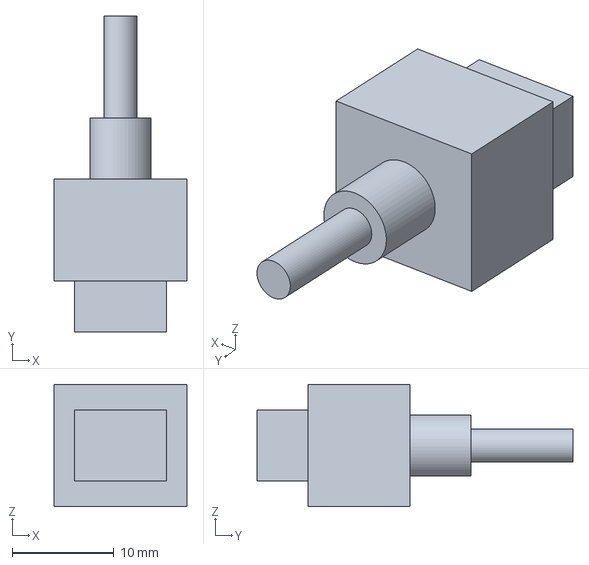
[picture p82: CAD file, 2026-10-05]
companion/parts/electronics/E12_MTS202_BU0014_provisional.step
13.0 x 31.0 x 12.0 mm
