zaidh-mech/project-zeno/companion/parts/printed/P03_Face_bezel.step

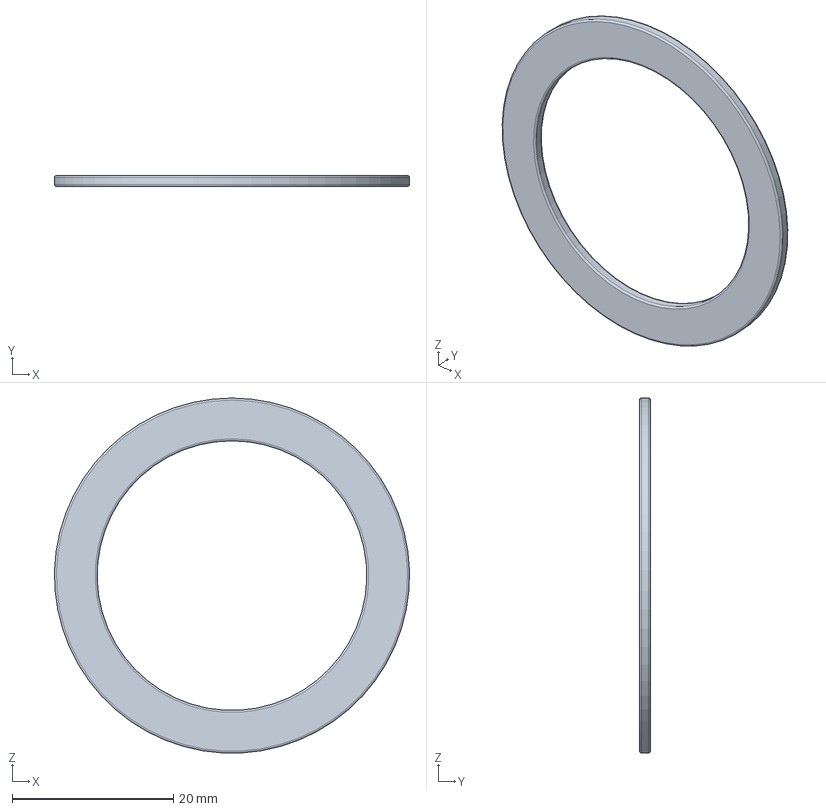
[picture p83: CAD file, 2026-10-05]
companion/parts/printed/P03_Face_bezel.step
44.0 x 1.40 x 44.0 mm
