zaidh-mech/project-zeno/companion/parts/electronics/E01_GC9A01_breakout_provisional.step

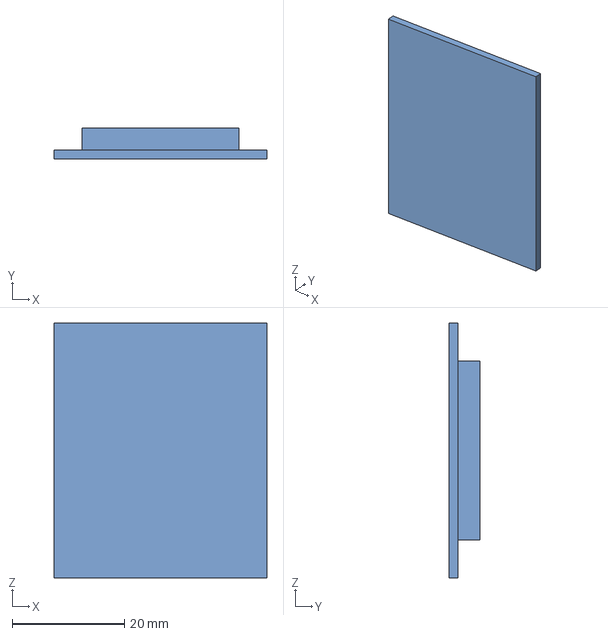
[picture p84: CAD file, 2026-10-05]
companion/parts/electronics/E01_GC9A01_breakout_provisional.step
38.0 x 5.60 x 45.5 mm
