zaidh-mech/project-zeno/companion/parts/printed/P12_USB_inlet_carrier.step

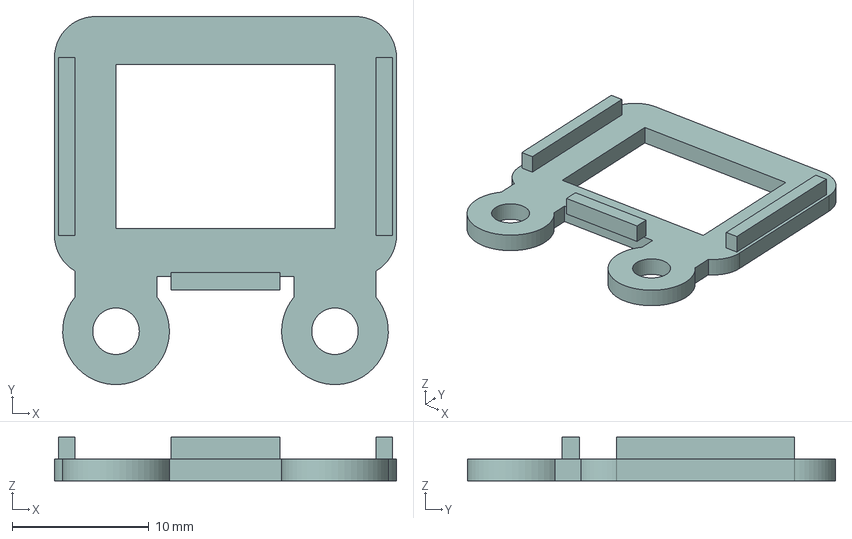
[picture p85: CAD file, 2026-10-05]
companion/parts/printed/P12_USB_inlet_carrier.step
25.0 x 26.9 x 3.20 mm
