zaidh-mech/project-zeno/companion/STL/P06_C3_snap_cap.stl

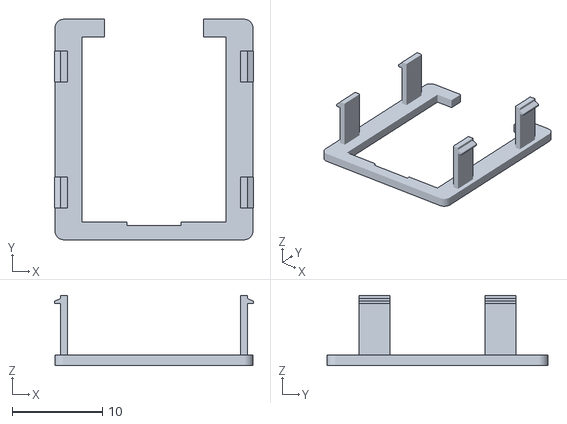
[picture p86: CAD file, 2026-10-05]
companion/STL/P06_C3_snap_cap.stl
22.1 x 24.5 x 7.80
