zaidh-mech/project-zeno/companion/parts/electronics/E10_18650_cell_BA0199_provisional.step

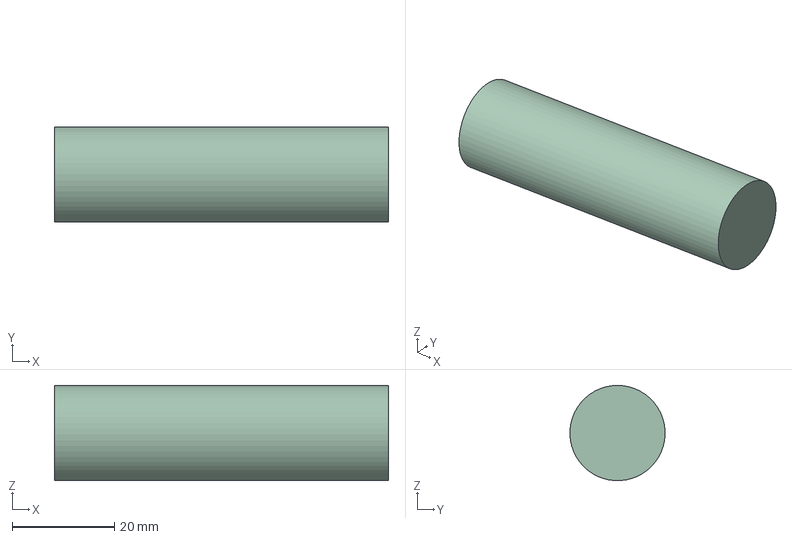
[picture p87: CAD file, 2026-10-05]
companion/parts/electronics/E10_18650_cell_BA0199_provisional.step
65.2 x 18.6 x 18.6 mm
