zaidh-mech/project-zeno/companion/STL/P01_Upper_shell.stl

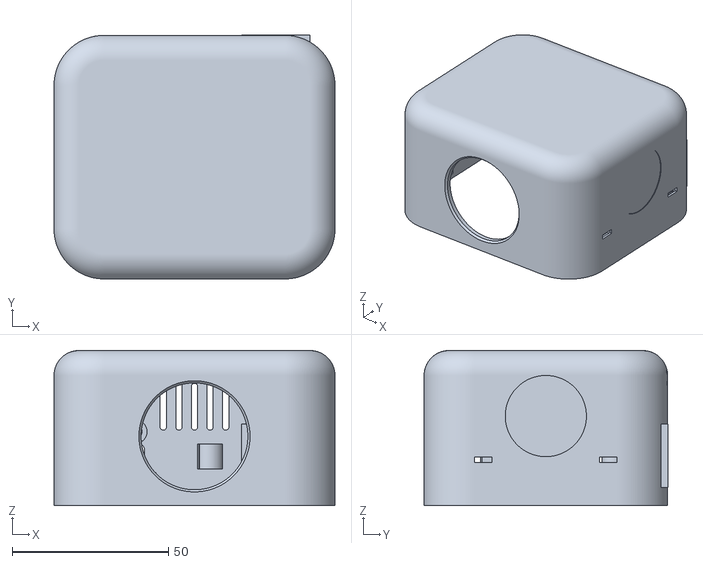
[picture p88: CAD file, 2026-10-05]
companion/STL/P01_Upper_shell.stl
90.0 x 78.1 x 49.7
