zaidh-mech/project-zeno/companion/parts/electronics/E07_TP4056_MD0744.step

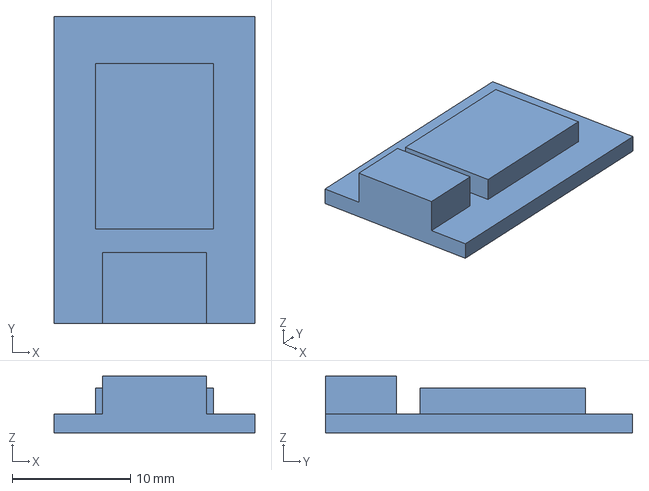
[picture p89: CAD file, 2026-10-05]
companion/parts/electronics/E07_TP4056_MD0744.step
17.0 x 26.0 x 4.80 mm
