zaidh-mech/project-zeno/companion/parts/electronics/E13_USBC_socket_provisional.step

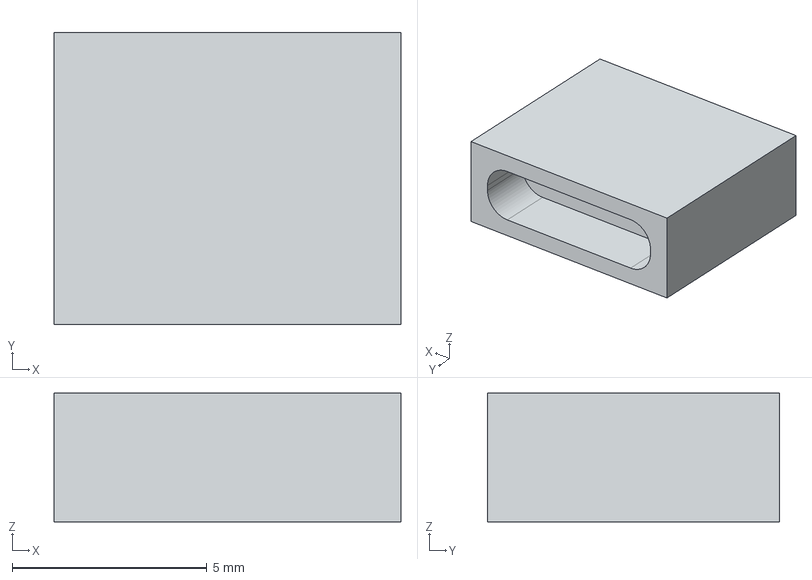
[picture p90: CAD file, 2026-10-05]
companion/parts/electronics/E13_USBC_socket_provisional.step
8.90 x 7.50 x 3.30 mm
