zaidh-mech/project-zeno/companion/STL/P07_Amplifier_snap_cap.stl

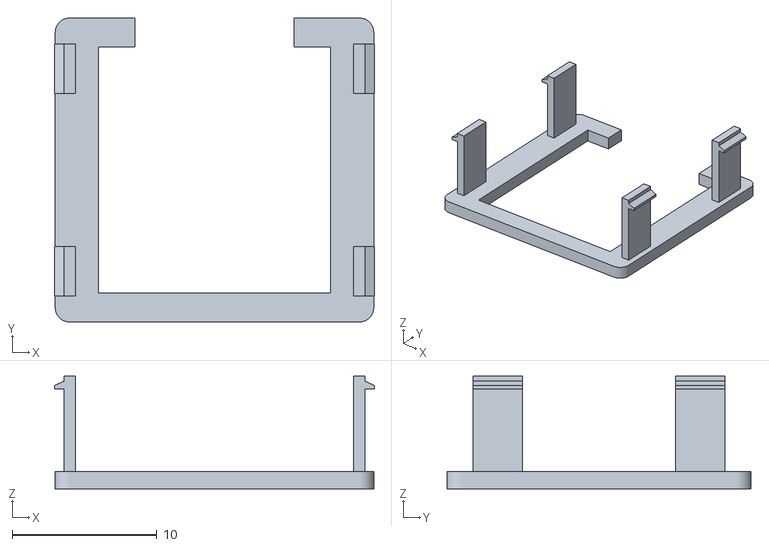
[picture p91: CAD file, 2026-10-05]
companion/STL/P07_Amplifier_snap_cap.stl
22.1 x 21.0 x 7.80
