zaidh-mech/project-zeno/companion/parts/electronics/E03_ESP32C3_SuperMini_A33.step

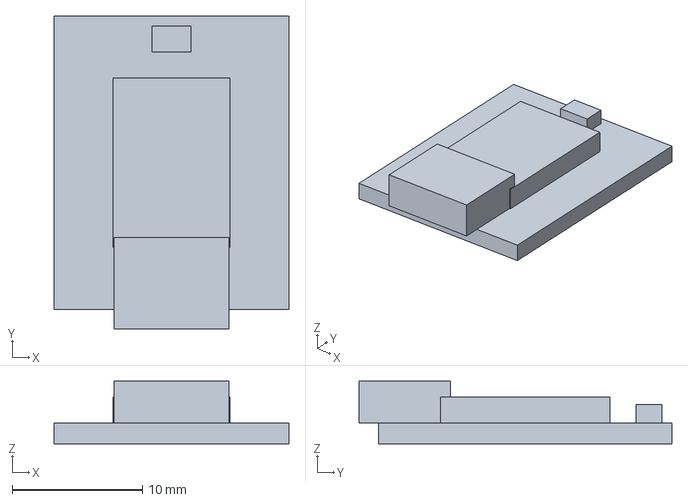
[picture p92: CAD file, 2026-10-05]
companion/parts/electronics/E03_ESP32C3_SuperMini_A33.step
18.0 x 24.0 x 4.80 mm
