zaidh-mech/project-zeno/companion/parts/electronics/E05_TTP223_MD0206_provisional.step

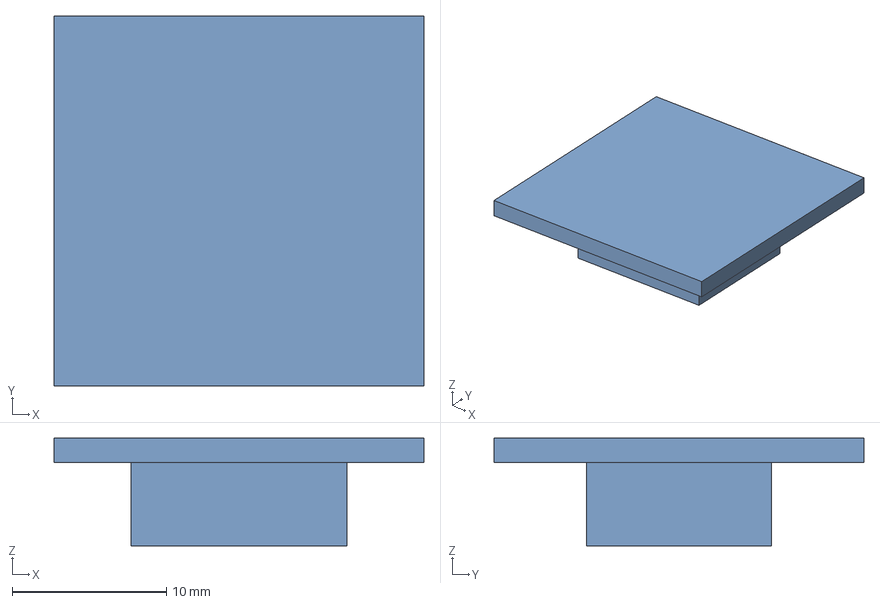
[picture p93: CAD file, 2026-10-05]
companion/parts/electronics/E05_TTP223_MD0206_provisional.step
24.0 x 24.0 x 7.00 mm
