zaidh-mech/project-zeno/companion/parts/hardware/H02_Speaker_gasket.step

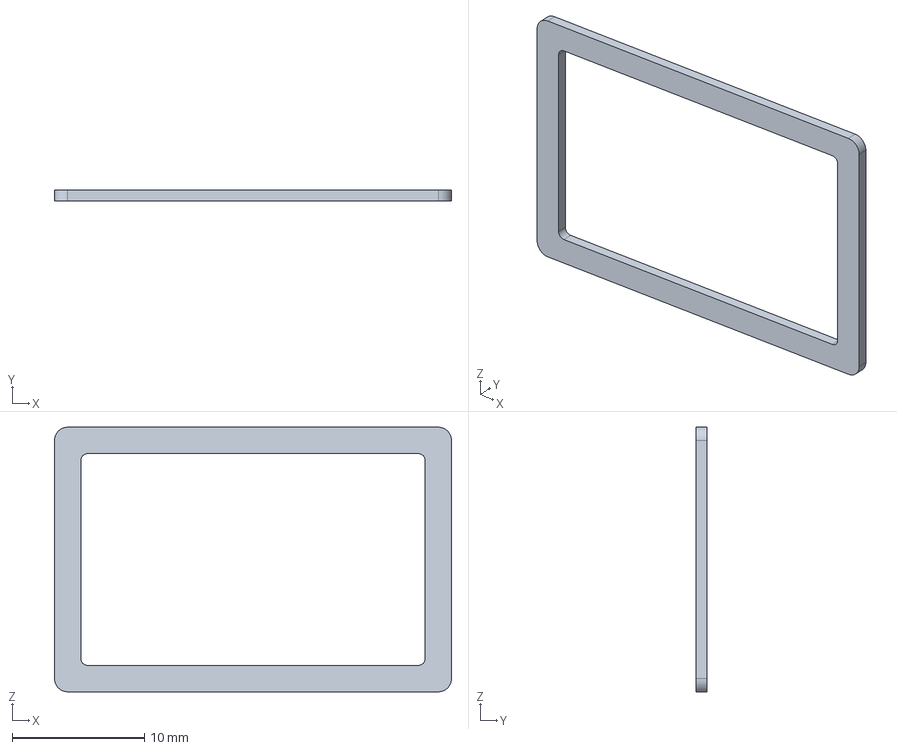
[picture p94: CAD file, 2026-10-05]
companion/parts/hardware/H02_Speaker_gasket.step
30.0 x 0.8 x 20.0 mm
