zaidh-mech/project-zeno/companion/parts/hardware/H94_Rubber_foot_4.step

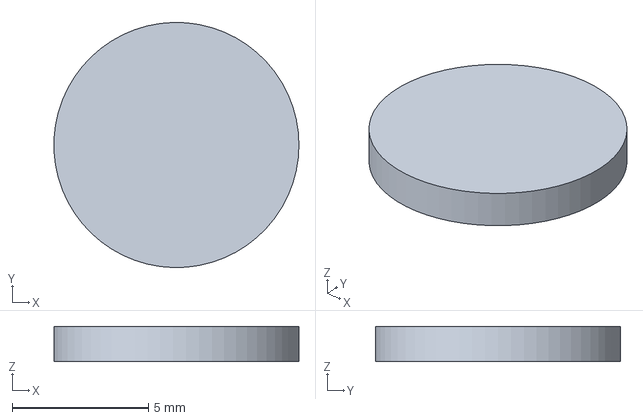
[picture p95: CAD file, 2026-10-05]
companion/parts/hardware/H94_Rubber_foot_4.step
8.99 x 9.00 x 1.30 mm
