zaidh-mech/project-zeno/companion/parts/hardware/H08_Power_pad_-20_-1.step

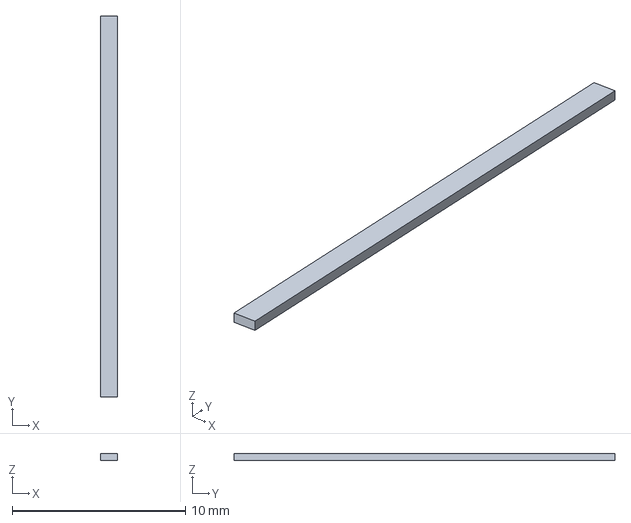
[picture p96: CAD file, 2026-10-05]
companion/parts/hardware/H08_Power_pad_-20_-1.step
1.00 x 22.0 x 0.4 mm
