zaidh-mech/project-zeno/companion/parts/hardware/H03_Cell_contact_L.step

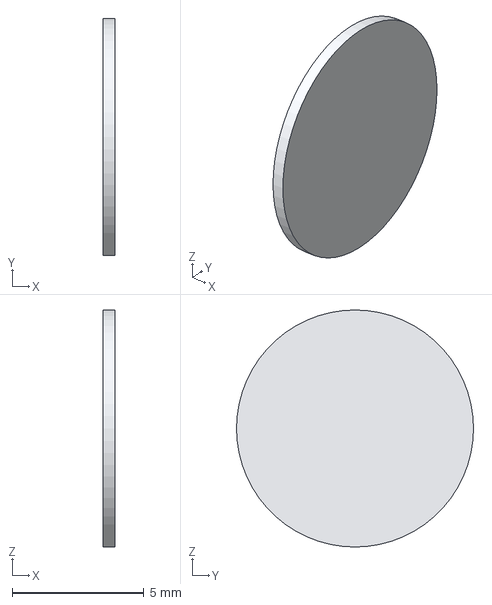
[picture p97: CAD file, 2026-10-05]
companion/parts/hardware/H03_Cell_contact_L.step
0.45 x 9.00 x 9.00 mm
