zaidh-mech/project-zeno/companion/parts/hardware/H06_USB_edge_pad_-34.5.step

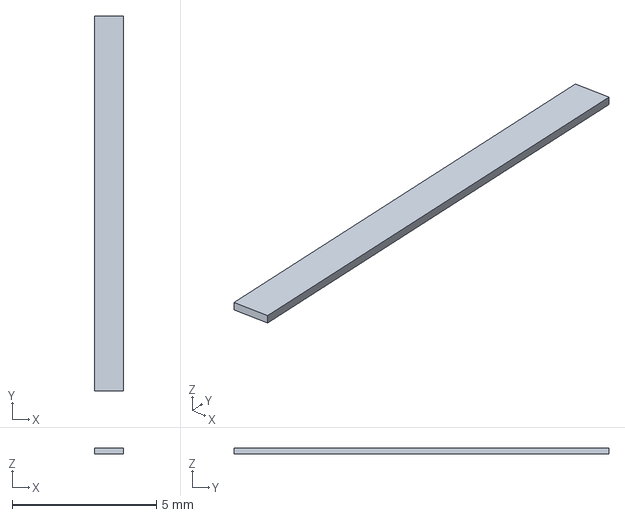
[picture p98: CAD file, 2026-10-05]
companion/parts/hardware/H06_USB_edge_pad_-34.5.step
1.00 x 13.0 x 0.2 mm
