zaidh-mech/project-zeno/companion/parts/hardware/H07_P07_Amplifier_snap_cap_pad_-1.step

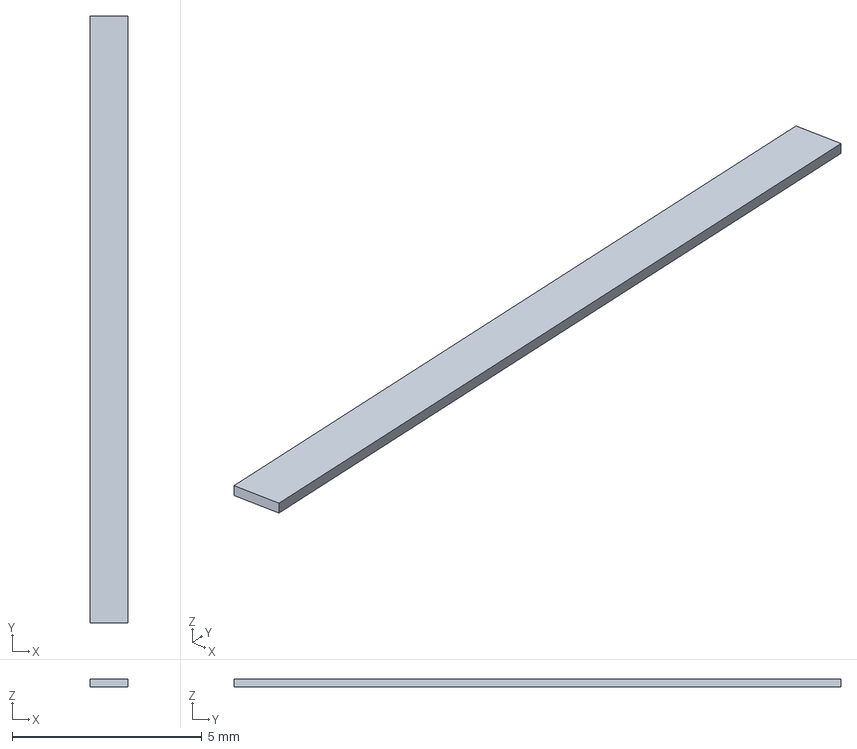
[picture p99: CAD file, 2026-10-05]
companion/parts/hardware/H07_P07_Amplifier_snap_cap_pad_-1.step
1.00 x 16.0 x 0.2 mm
