zaidh-mech/project-zeno/companion/parts/hardware/H07_P06_C3_snap_cap_pad_-1.step

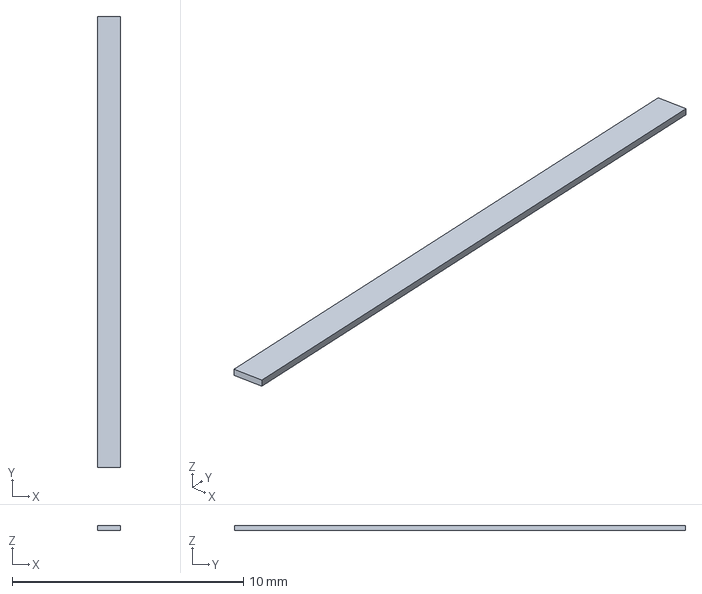
[picture p100: CAD file, 2026-10-05]
companion/parts/hardware/H07_P06_C3_snap_cap_pad_-1.step
1.00 x 19.5 x 0.2 mm
