zaidh-mech/project-zeno/companion/parts/hardware/H00_Seam_anti_rattle_foam.step

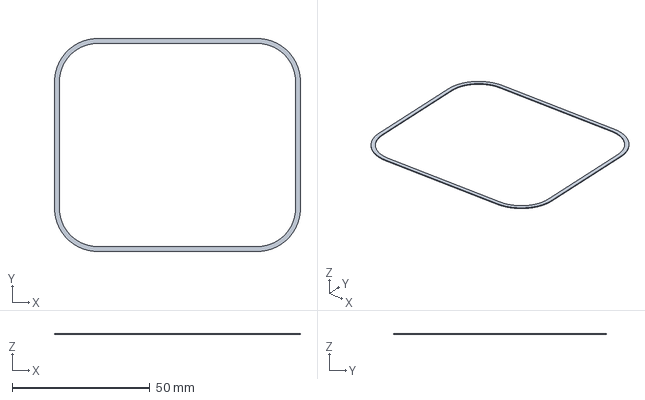
[picture p101: CAD file, 2026-10-05]
companion/parts/hardware/H00_Seam_anti_rattle_foam.step
89.4 x 77.4 x 0.35 mm
