zaidh-mech/project-zeno/companion/parts/hardware/H05_LCD_perimeter_gasket.step

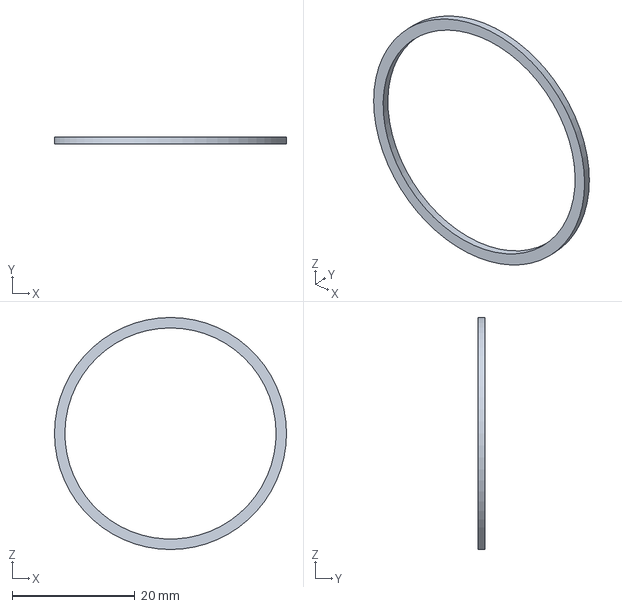
[picture p102: CAD file, 2026-10-05]
companion/parts/hardware/H05_LCD_perimeter_gasket.step
37.8 x 1.10 x 37.8 mm
