zaidh-mech/project-zeno/companion/drawings/01_Assembled.png

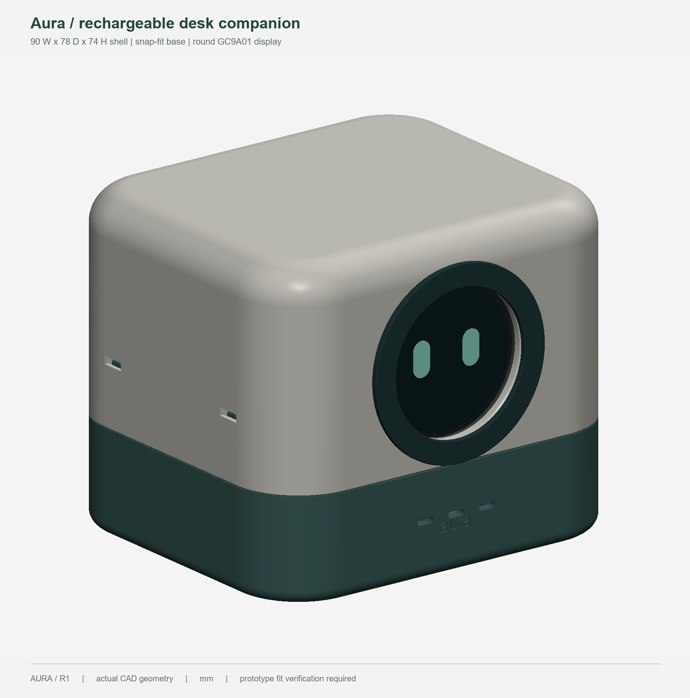
companion/drawings/01_Assembled.png
