zaidh-mech/project-zeno/assets/photos/20240722_174317.jpg

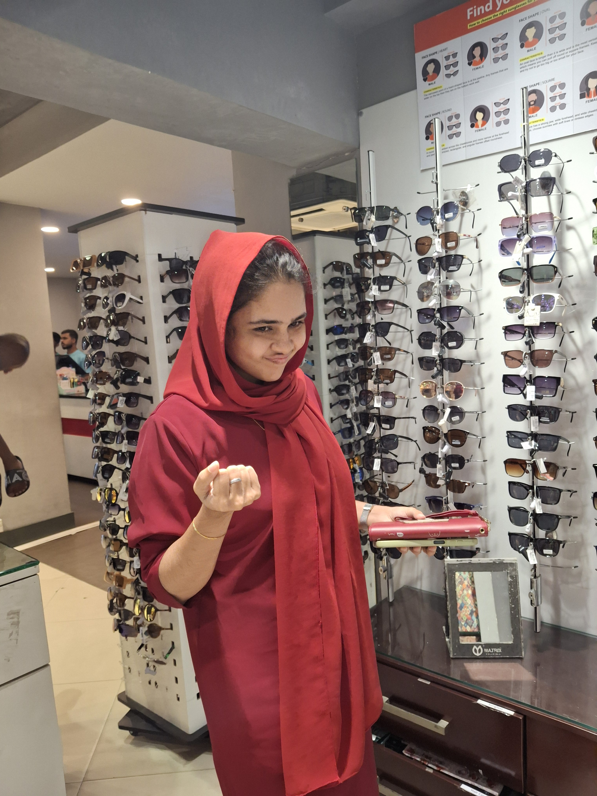
assets/photos/20240722_174317.jpg
