zaidh-mech/project-zeno/assets/photos/20250816_143933.jpg

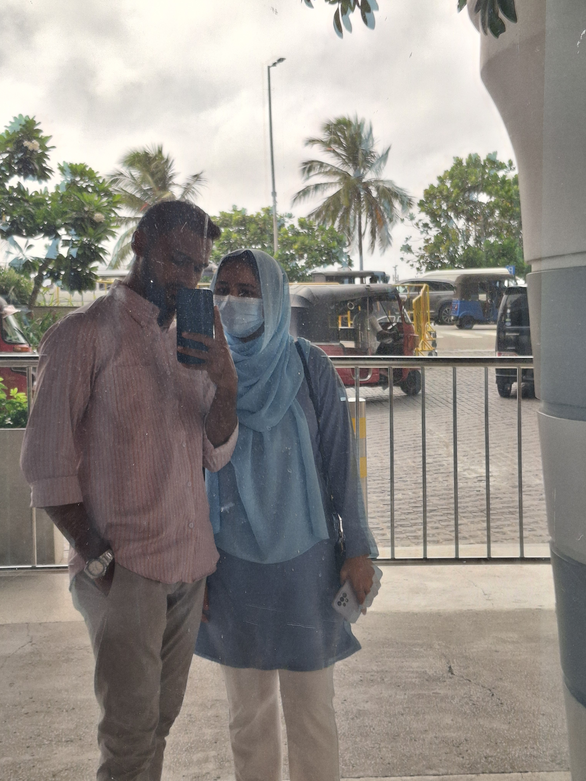
assets/photos/20250816_143933.jpg
