zaidh-mech/project-zeno/assets/photos/20250816_165613.jpg

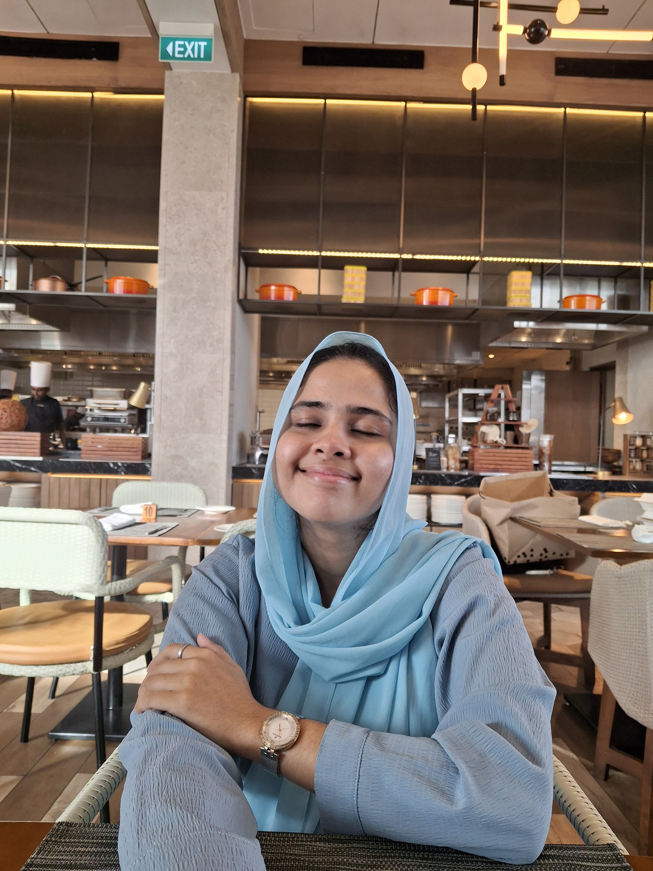
assets/photos/20250816_165613.jpg
