zaidh-mech/project-zeno/assets/photos/20250816_171847.jpg

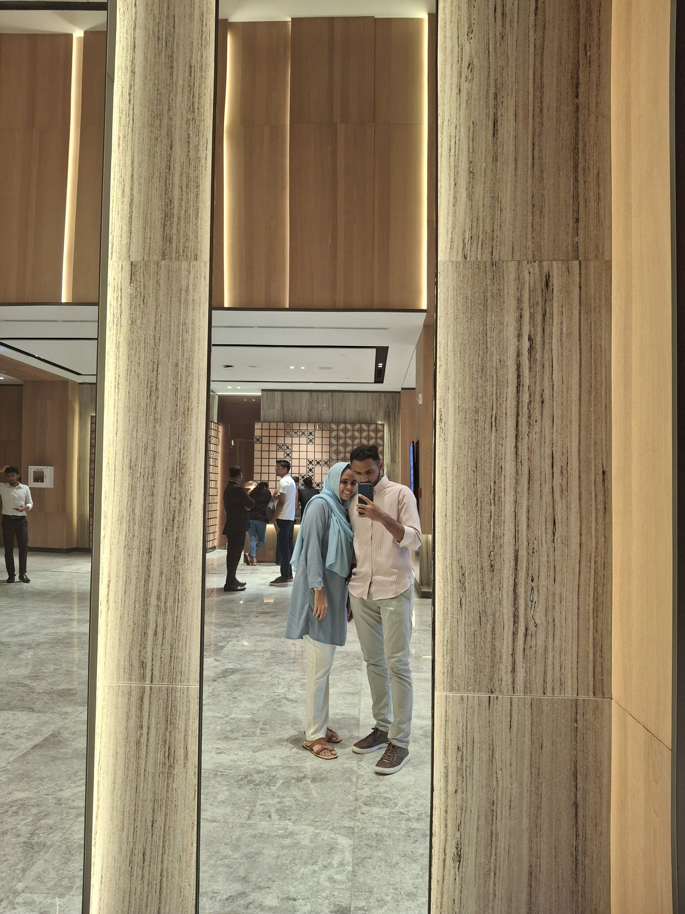
assets/photos/20250816_171847.jpg
