zaidh-mech/project-zeno/assets/photos/20250816_171916.jpg

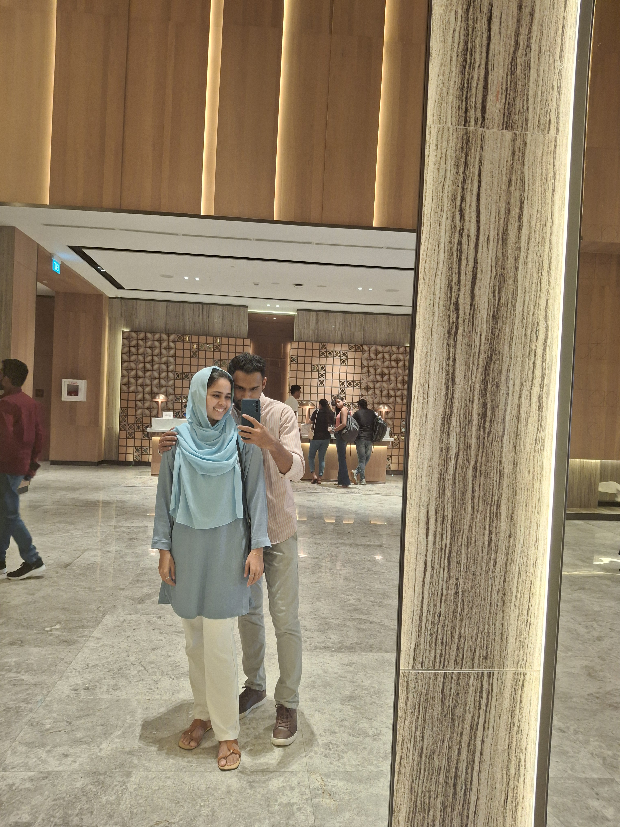
assets/photos/20250816_171916.jpg
